danjulio/lepton/ESP32/DesktopApp/pictures/graph_window.png

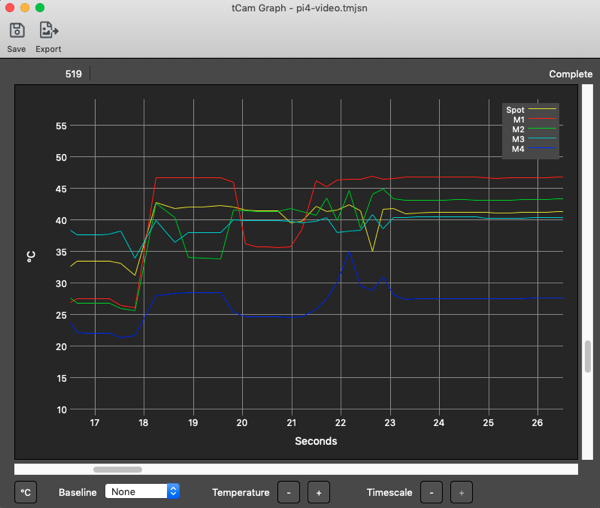
ESP32/DesktopApp/pictures/graph_window.png
