danjulio/lepton/ESP32/tCam-Mini/pictures/hw_if_spi_data.png

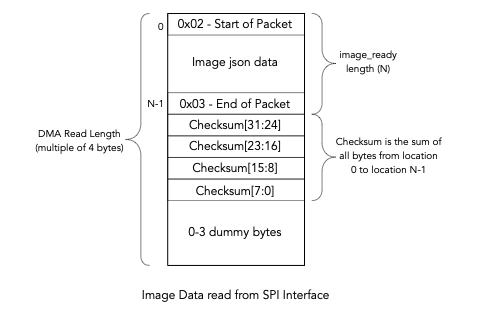
ESP32/tCam-Mini/pictures/hw_if_spi_data.png
