danjulio/lepton/ESP32/tCam-Mini/pictures/tcam_mini_pcb_r1.png

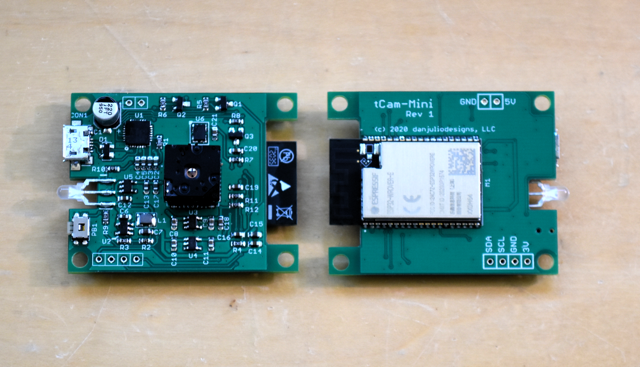
ESP32/tCam-Mini/pictures/tcam_mini_pcb_r1.png
