danjulio/lepton/ESP32/tCam-Mini/pictures/tcam_mini_pcb_r2.png

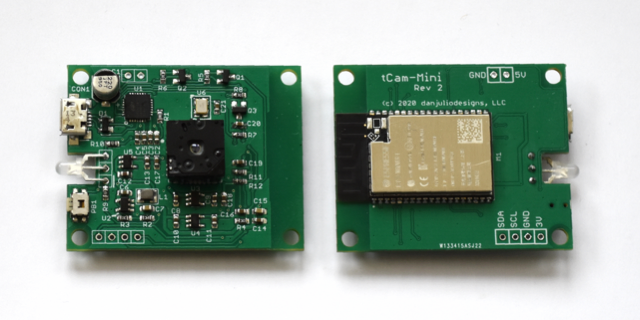
ESP32/tCam-Mini/pictures/tcam_mini_pcb_r2.png
