danjulio/lepton/ESP32/tCam-Mini/pictures/tcam_mini_prototype.png

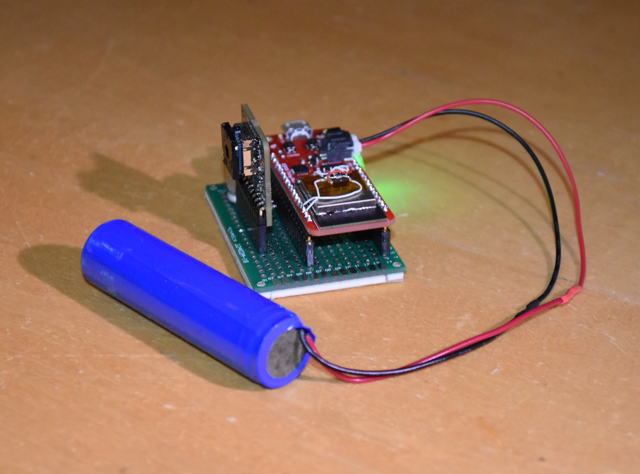
ESP32/tCam-Mini/pictures/tcam_mini_prototype.png
