danjulio/lepton/ESP32/tCam-Mini/pictures/ttgo_based_tcam_mini.png

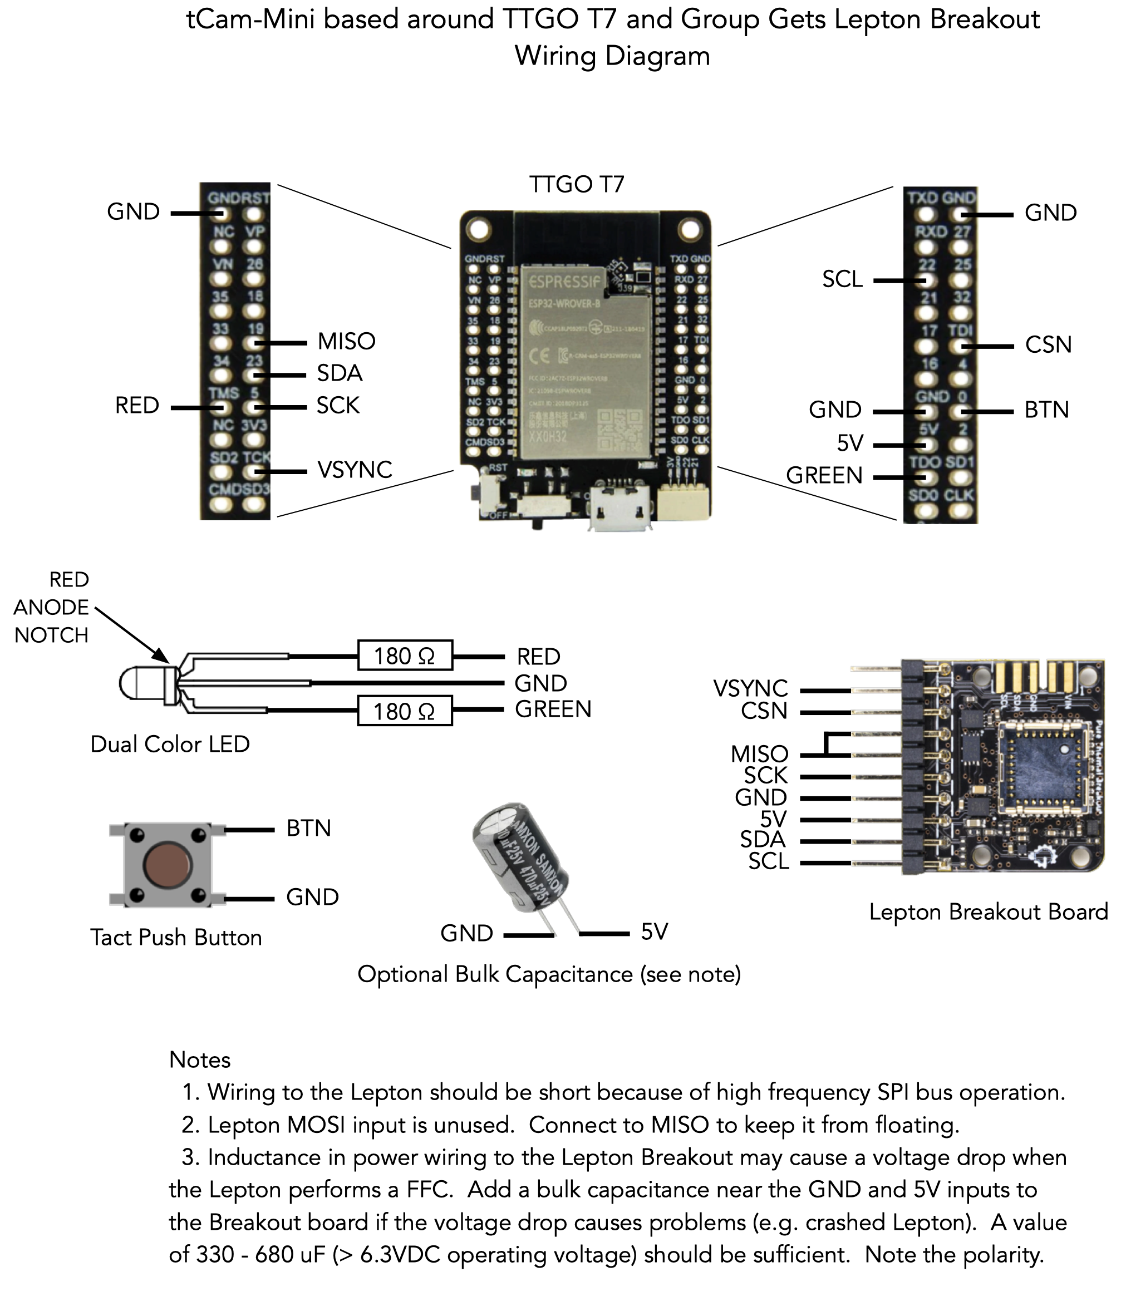
ESP32/tCam-Mini/pictures/ttgo_based_tcam_mini.png
