danjulio/lepton/ESP32/tCam-Mini/pictures/ttgo_version_side.png

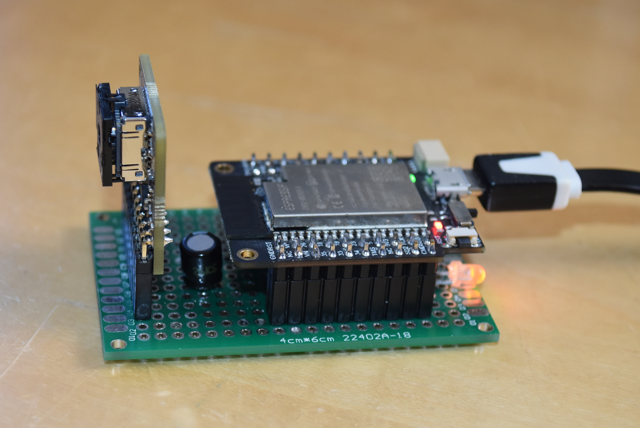
ESP32/tCam-Mini/pictures/ttgo_version_side.png
