danjulio/lepton/ESP32/tCam-Mini/pictures/ttgo_version_top_bot.png

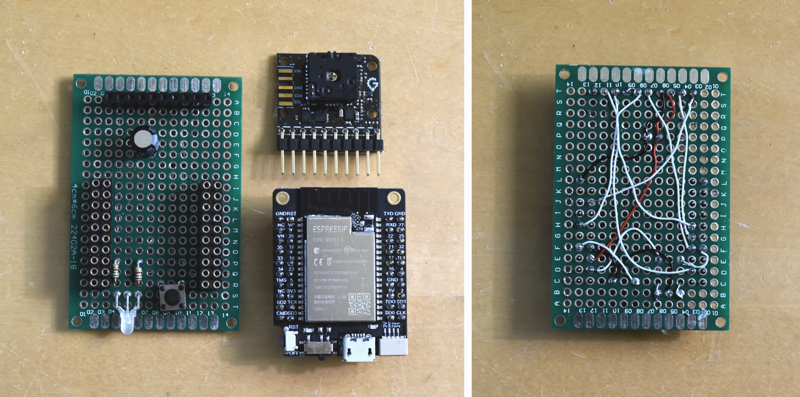
ESP32/tCam-Mini/pictures/ttgo_version_top_bot.png
