danjulio/lepton/ESP32/WebApp/pictures/tcam_analysis.png

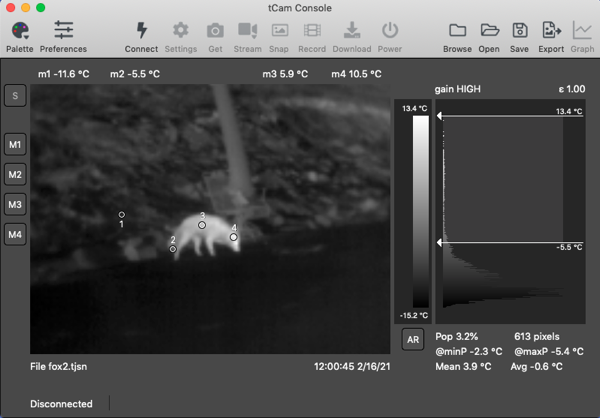
ESP32/WebApp/pictures/tcam_analysis.png
