danjulio/lepton/ESP32/WebApp/pictures/tcam_web_add_camera.png

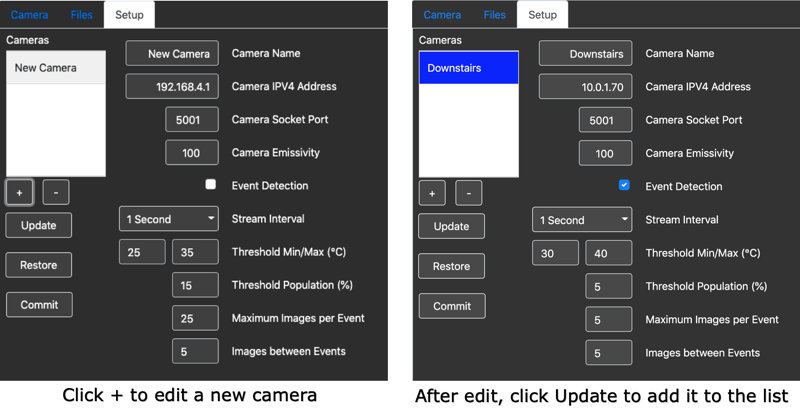
ESP32/WebApp/pictures/tcam_web_add_camera.png
