danjulio/lepton/ESP32/WebApp/pictures/tcam_web_files.png

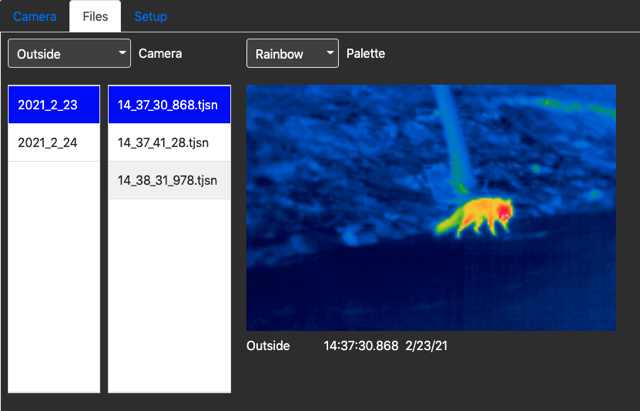
ESP32/WebApp/pictures/tcam_web_files.png
