danjulio/lepton/ESP32/WebApp/pictures/tcam_web_viewer_annotated.png

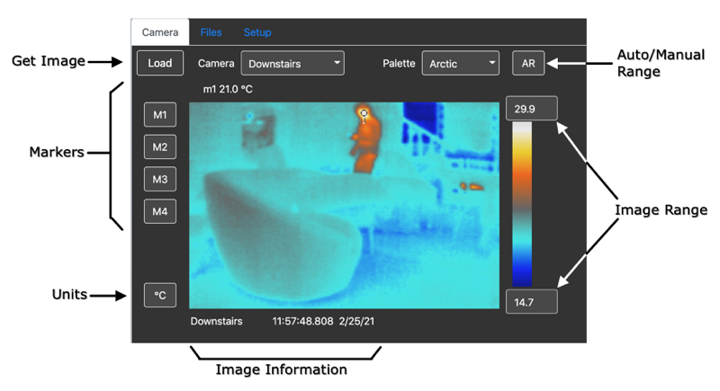
ESP32/WebApp/pictures/tcam_web_viewer_annotated.png
