danjulio/lepton/teensy3/LeptonSDKEmb32OEM/LeptonSDKEmb32OEM.cpp

/*******************************************************************************
**
**   File NAME: LeptonSDKEmb32OEM.cpp
**
**   CREATED: 6/12/2018
**
**   DESCRIPTION: Lepton SDK Module ported to Arduino
**
**   HISTORY: 6/12/2018 DJD - Initial Draft
**           11/22/2019 DJD - Support for ESP32
**
**   Based on FLIR Systems Inc source code.  Their license is copied below
**   and forms the license for this code.
**
**      Copyright 2011,2012,2013,2014 FLIR Systems - Commercial
**      Vision Systems.  All rights reserved.
**
**      Proprietary - PROPRIETARY - FLIR Systems Inc.
**
**      This document is controlled to FLIR Technology Level 2.
**      The information contained in this document pertains to a
**      dual use product Controlled for export by the Export
**      Administration Regulations (EAR). Diversion contrary to
**      US law is prohibited.  US Department of Commerce
**      authorization is not required prior to export or
**      transfer to foreign persons or parties unless otherwise
**      prohibited.
**
**      Redistribution and use in source and binary forms, with
**      or without modification, are permitted provided that the
**      following conditions are met:
**
**      Redistributions of source code must retain the above
**      copyright notice, this list of conditions and the
**      following disclaimer.
**
**      Redistributions in binary form must reproduce the above
**      copyright notice, this list of conditions and the
**      following disclaimer in the documentation and/or other
**      materials provided with the distribution.
**
**      Neither the name of the FLIR Systems Corporation nor the
**      names of its contributors may be used to endorse or
**      promote products derived from this software without
**      specific prior written permission.
**
**      THIS SOFTWARE IS PROVIDED BY THE COPYRIGHT HOLDERS AND
**      CONTRIBUTORS "AS IS" AND ANY EXPRESS OR IMPLIED
**      WARRANTIES, INCLUDING, BUT NOT LIMITED TO, THE IMPLIED
**      WARRANTIES OF MERCHANTABILITY AND FITNESS FOR A
**      PARTICULAR PURPOSE ARE DISCLAIMED. IN NO EVENT SHALL THE
**      COPYRIGHT OWNER OR CONTRIBUTORS BE LIABLE FOR ANY
**      DIRECT, INDIRECT, INCIDENTAL, SPECIAL, EXEMPLARY, OR
**      CONSEQUENTIAL DAMAGES (INCLUDING, BUT NOT LIMITED TO,
**      PROCUREMENT OF SUBSTITUTE GOODS OR SERVICES; LOSS OF
**      USE, DATA, OR PROFITS; OR BUSINESS INTERRUPTION) HOWEVER
**      CAUSED AND ON ANY THEORY OF LIABILITY, WHETHER IN
**      CONTRACT, STRICT LIABILITY, OR TORT (INCLUDING
**      NEGLIGENCE OR OTHERWISE) ARISING IN ANY WAY OUT OF THE
**      USE OF THIS SOFTWARE, EVEN IF ADVISED OF THE POSSIBILITY
**      OF SUCH DAMAGE.
**
*******************************************************************************/
#include "LeptonSDKEmb32OEM.h"
#include <Arduino.h>
#if defined(CORE_TEENSY)
#include <i2c_t3.h>
#else
#include <Wire.h> 
#endif

#if (USE_BORESIGHT_MEASUREMENT_FUNCTIONS == 1)
#include "math.h"
#endif

LeptonSDKEmb32OEM::LeptonSDKEmb32OEM()
{
}


/**************************************/
/*                AGC                 */
/**************************************/

/**
 * Retrieves the current AGC Enable state from the Camera. The 
 * AGC enable state turns AGC On (enabled) or OFF (disabled).   
 * 
 * @param agcEnableStatePtr
 *               Pointer to variable to update with the camera's
 *               current state.
 *               Range:
 *                  LEP_AGC_DISABLE=0
 *                  LEP_AGC_ENABLE =1
 * 
 * @return LEP_OK if all goes well, otherwise an error code.
 */
LEP_RESULT LeptonSDKEmb32OEM::LEP_GetAgcEnableState( LEP_CAMERA_PORT_DESC_T_PTR portDescPtr,
                                  LEP_AGC_ENABLE_E_PTR agcEnableStatePtr )
{
   LEP_RESULT  result = LEP_OK;
   LEP_UINT16 attributeWordLength = 2; /* attribute is an enum, so 32-bit value */

   /* Validate Parameter(s)
   */
   if( agcEnableStatePtr == NULL )
   {
      return( LEP_BAD_ARG_POINTER_ERROR );
   }

   /* Perform Command
   ** Read the Camera's AGC Enable State
   */
   result = LEP_GetAttribute( portDescPtr,
                              ( LEP_COMMAND_ID )LEP_CID_AGC_ENABLE_STATE,
                              ( LEP_ATTRIBUTE_T_PTR )agcEnableStatePtr,
                              attributeWordLength );
   return( result );
}

/**
 * Sets the current AGC Enable state on the Camera.  The 
 * AGC enable state turns AGC On (enabled) or OFF (disabled).
 * 
 * @param agcEnableState 
 *             Specifies the enable state to set the camera' AGC
 *             Range:
 *                LEP_AGC_DISABLE=0
 *                LEP_AGC_ENABLE =1
 * 
 * @return LEP_OK if all goes well, otherwise an error code.
 */
LEP_RESULT LeptonSDKEmb32OEM::LEP_SetAgcEnableState( LEP_CAMERA_PORT_DESC_T_PTR portDescPtr,
                                  LEP_AGC_ENABLE_E agcEnableState )
{
   LEP_RESULT  result = LEP_OK;
   LEP_UINT16 attributeWordLength = 2; /* 2 16-bit value */

   _LEP_data[1] = 0;
   _LEP_data[0] = (LEP_UINT16) agcEnableState;

   /* Validate Parameter(s)
   */
   if( agcEnableState >= LEP_END_AGC_ENABLE )
   {
      return( LEP_RANGE_ERROR );
   }

   /* Perform Command
   ** Writing the Camera's AGC Enable State
   */
   result = LEP_SetAttribute( portDescPtr,
                              ( LEP_COMMAND_ID )LEP_CID_AGC_ENABLE_STATE,
                              ( LEP_ATTRIBUTE_T_PTR ) & _LEP_data,
                              attributeWordLength );
   return( result );
}




LEP_RESULT LeptonSDKEmb32OEM::LEP_GetAgcPolicy( LEP_CAMERA_PORT_DESC_T_PTR portDescPtr,
                             LEP_AGC_POLICY_E_PTR agcPolicyPtr )
{
   LEP_RESULT  result = LEP_OK;
   LEP_UINT16 attributeWordLength = 2; /* 2 16-bit value */

   /* Validate Parameter(s)
   */
   if( agcPolicyPtr == NULL )
   {
      return( LEP_BAD_ARG_POINTER_ERROR );
   }

   /* Perform Command
   ** Reading the Camera's AGC Policy
   */
   result = LEP_GetAttribute(  portDescPtr,
                              ( LEP_COMMAND_ID )LEP_CID_AGC_POLICY,
                              ( LEP_ATTRIBUTE_T_PTR )agcPolicyPtr,
                              attributeWordLength );
   return( result );
}

LEP_RESULT LeptonSDKEmb32OEM::LEP_SetAgcPolicy( LEP_CAMERA_PORT_DESC_T_PTR portDescPtr,
                             LEP_AGC_POLICY_E agcPolicy )
{
   LEP_RESULT  result = LEP_OK;
   LEP_UINT16 attributeWordLength = 2; /* 2 16-bit value */

   _LEP_data[1] = 0;
   _LEP_data[0] = (LEP_UINT16) agcPolicy;

   /* Bounds Check
   */
   if( agcPolicy >= LEP_END_AGC_POLICY )
   {
      return( LEP_RANGE_ERROR );
   }

   /* Perform Command
   ** Writing the Camera's AGC Policy
   */
   result = LEP_SetAttribute( portDescPtr,
                              ( LEP_COMMAND_ID )LEP_CID_AGC_POLICY,
                              ( LEP_ATTRIBUTE_T_PTR ) & _LEP_data,
                              attributeWordLength );
   return( result );
}



LEP_RESULT LeptonSDKEmb32OEM::LEP_GetAgcROI( LEP_CAMERA_PORT_DESC_T_PTR portDescPtr,
                          LEP_AGC_ROI_T_PTR agcROIPtr )
{
   LEP_RESULT  result = LEP_OK;
   LEP_UINT16 attributeWordLength = 4; /* four 16-bit values */

   /* Validate Parameter(s)
   */
   if( agcROIPtr == NULL )
   {
      return( LEP_BAD_ARG_POINTER_ERROR );
   }

   /* Perform Command
   ** Reading the Camera's AGC ROI
   */
   result = LEP_GetAttribute( portDescPtr,
                              ( LEP_COMMAND_ID )LEP_CID_AGC_ROI,
                              ( LEP_ATTRIBUTE_T_PTR )agcROIPtr,
                              attributeWordLength );
   //return(sizeof(*agcROIPtr));
   return( result );
}


LEP_RESULT LeptonSDKEmb32OEM::LEP_SetAgcROI( LEP_CAMERA_PORT_DESC_T_PTR portDescPtr,
                          LEP_AGC_ROI_T agcROI )
{
   LEP_RESULT  result = LEP_OK;
   LEP_UINT16 attributeWordLength = 4; /* four 16-bit values */

   _LEP_data[3] = agcROI.endRow;
   _LEP_data[2] = agcROI.endCol;
   _LEP_data[1] = agcROI.startRow;
   _LEP_data[0] = agcROI.startCol;

   /* Perform Command
   ** Writing the Camera's AGC ROI
   */
   result = LEP_SetAttribute( portDescPtr,
                              ( LEP_COMMAND_ID )LEP_CID_AGC_ROI,
                              ( LEP_ATTRIBUTE_T_PTR ) & _LEP_data,
                              attributeWordLength );


   return( result );
}

LEP_RESULT LeptonSDKEmb32OEM::LEP_GetAgcLinearHistogramClipPercent( LEP_CAMERA_PORT_DESC_T_PTR portDescPtr,
                                                 LEP_UINT16 *agcLinearHistogramClipPercentPtr )
{
   LEP_RESULT  result = LEP_OK;
   LEP_UINT16 attributeWordLength = 1; /* single 16-bit value */

   /* Validate Parameter(s)
   */
   if( agcLinearHistogramClipPercentPtr == NULL )
   {
      return( LEP_BAD_ARG_POINTER_ERROR );
   }

   /* Perform Command
   ** Reading the Camera's AGC Linear Histogram Clip Percent
   */
   result = LEP_GetAttribute( portDescPtr,
                              ( LEP_COMMAND_ID )LEP_CID_AGC_HISTOGRAM_CLIP_PERCENT,
                              ( LEP_ATTRIBUTE_T_PTR )agcLinearHistogramClipPercentPtr,
                              attributeWordLength );
   return( result );
}

LEP_RESULT LeptonSDKEmb32OEM::LEP_SetAgcLinearHistogramClipPercent( LEP_CAMERA_PORT_DESC_T_PTR portDescPtr,
                                                 LEP_UINT16 agcLinearHistogramClipPercent )
{
   LEP_RESULT  result = LEP_OK;
   LEP_UINT16 attributeWordLength = 1; /* single 16-bit value */


   /* Perform Command
   ** Writing the Camera's AGC Linear Histogram Clip Percent
   */
   result = LEP_SetAttribute( portDescPtr,
                              ( LEP_COMMAND_ID )LEP_CID_AGC_HISTOGRAM_CLIP_PERCENT,
                              ( LEP_ATTRIBUTE_T_PTR ) & agcLinearHistogramClipPercent,
                              attributeWordLength
                              );
   return( result );
}


LEP_RESULT LeptonSDKEmb32OEM::LEP_GetAgcLinearHistogramTailSize( LEP_CAMERA_PORT_DESC_T_PTR portDescPtr,
                                              LEP_UINT16 *agcLinearHistogramTailSizePtr )
{
   LEP_RESULT  result = LEP_OK;
   LEP_UINT16 attributeWordLength = 1; /* single 16-bit value */

   /* Validate Parameter(s)
   */
   if( agcLinearHistogramTailSizePtr == NULL )
   {
      return( LEP_BAD_ARG_POINTER_ERROR );
   }

   /* Perform Command
   ** Reading the Camera's AGC Linear Histogram Tail Size
   */
   result = LEP_GetAttribute( portDescPtr,
                              ( LEP_COMMAND_ID )LEP_CID_AGC_HISTOGRAM_TAIL_SIZE,
                              ( LEP_ATTRIBUTE_T_PTR )agcLinearHistogramTailSizePtr,
                              attributeWordLength );
   return( result );
}


LEP_RESULT LeptonSDKEmb32OEM::LEP_SetAgcLinearHistogramTailSize( LEP_CAMERA_PORT_DESC_T_PTR portDescPtr,
                                              LEP_UINT16 agcLinearHistogramTailSize )
{
   LEP_RESULT  result = LEP_OK;
   LEP_UINT16 attributeWordLength = 1; /* single 16-bit value */


   /* Perform Command
   ** Writing the Camera's AGC Linear Histogram Clip Percent
   */
   result = LEP_SetAttribute( portDescPtr,
                              ( LEP_COMMAND_ID )LEP_CID_AGC_HISTOGRAM_TAIL_SIZE,
                              ( LEP_ATTRIBUTE_T_PTR ) & agcLinearHistogramTailSize,
                              attributeWordLength
                              );
   return( result );
}


LEP_RESULT LeptonSDKEmb32OEM::LEP_GetAgcHistogramStatistics( LEP_CAMERA_PORT_DESC_T_PTR portDescPtr,
                                          LEP_AGC_HISTOGRAM_STATISTICS_T_PTR *agcHistogramStatisticsPtr )
{
   LEP_RESULT  result = LEP_OK;
   LEP_UINT16 attributeWordLength = 4; /* four 16-bit values */

   /* Validate Parameter(s)
   */
   if( agcHistogramStatisticsPtr == NULL )
   {
      return( LEP_BAD_ARG_POINTER_ERROR );
   }

   /* Perform Command
   ** Reading the Camera's AGC Linear Histogram Statistics
   */
   result = LEP_GetAttribute( portDescPtr,
                              ( LEP_COMMAND_ID )LEP_CID_AGC_STATISTICS,
                              ( LEP_ATTRIBUTE_T_PTR )agcHistogramStatisticsPtr,
                              attributeWordLength );
   return( result );
}



/* Linear Policy Controls
*/

LEP_RESULT LeptonSDKEmb32OEM::LEP_GetAgcLinearMaxGain( LEP_CAMERA_PORT_DESC_T_PTR portDescPtr,
                                    LEP_UINT16 *agcLinearMaxGainPtr )
{
   LEP_RESULT  result = LEP_OK;
   LEP_UINT16 attributeWordLength = 1; /* single 16-bit value */

   /* Validate Parameter(s)
   */
   if( agcLinearMaxGainPtr == NULL )
   {
      return( LEP_BAD_ARG_POINTER_ERROR );
   }

   /* Perform Command
   ** Reading the Camera's AGC Linear Max Gain
   */
   result = LEP_GetAttribute( portDescPtr,
                              ( LEP_COMMAND_ID )LEP_CID_AGC_LINEAR_MAX_GAIN,
                              ( LEP_ATTRIBUTE_T_PTR )agcLinearMaxGainPtr,
                              attributeWordLength );
   return( result );
}


LEP_RESULT LeptonSDKEmb32OEM::LEP_SetAgcLinearMaxGain( LEP_CAMERA_PORT_DESC_T_PTR portDescPtr,
                                    LEP_UINT16 agcLinearMaxGain )
{
   LEP_RESULT  result = LEP_OK;
   LEP_UINT16 attributeWordLength = 1; /* single 16-bit value */


   /* Perform Command
   ** Writing the Camera's AGC Linear Max Gain
   */
   result = LEP_SetAttribute( portDescPtr,
                              ( LEP_COMMAND_ID )LEP_CID_AGC_LINEAR_MAX_GAIN,
                              ( LEP_ATTRIBUTE_T_PTR ) & agcLinearMaxGain,
                              attributeWordLength
                              );
   return( result );
}


LEP_RESULT LeptonSDKEmb32OEM::LEP_GetAgcLinearMidPoint( LEP_CAMERA_PORT_DESC_T_PTR portDescPtr,
                                     LEP_UINT16 *agcLinearMidPointPtr )
{
   LEP_RESULT  result = LEP_OK;
   LEP_UINT16 attributeWordLength = 1; /* single 16-bit value */

   /* Validate Parameter(s)
   */
   if( agcLinearMidPointPtr == NULL )
   {
      return( LEP_BAD_ARG_POINTER_ERROR );
   }

   /* Perform Command
   ** Reading the Camera's AGC Linear Midpoint
   */
   result = LEP_GetAttribute( portDescPtr,
                              ( LEP_COMMAND_ID )LEP_CID_AGC_LINEAR_MIDPOINT,
                              ( LEP_ATTRIBUTE_T_PTR )agcLinearMidPointPtr,
                              attributeWordLength );
   return( result );
}


LEP_RESULT LeptonSDKEmb32OEM::LEP_SetAgcLinearMidPoint( LEP_CAMERA_PORT_DESC_T_PTR portDescPtr,
                                     LEP_UINT16 agcLinearMidPoint )
{
   LEP_RESULT  result = LEP_OK;
   LEP_UINT16 attributeWordLength = 1; /* single 16-bit value */


   /* Perform Command
   ** Writing the Camera's AGC Linear Midpoint
   */
   result = LEP_SetAttribute( portDescPtr,
                              ( LEP_COMMAND_ID )LEP_CID_AGC_LINEAR_MIDPOINT,
                              ( LEP_ATTRIBUTE_T_PTR ) & agcLinearMidPoint,
                              attributeWordLength
                              );
   return( result );
}


LEP_RESULT LeptonSDKEmb32OEM::LEP_GetAgcLinearDampeningFactor( LEP_CAMERA_PORT_DESC_T_PTR portDescPtr,
                                            LEP_UINT16 *agcLinearDampeningFactorPtr )
{
   LEP_RESULT  result = LEP_OK;
   LEP_UINT16 attributeWordLength = 1; /* single 16-bit value */

   /* Validate Parameter(s)
   */
   if( agcLinearDampeningFactorPtr == NULL )
   {
      return( LEP_BAD_ARG_POINTER_ERROR );
   }

   /* Perform Command
   ** Reading the Camera's AGC Linear Dampening Factor
   */
   result = LEP_GetAttribute( portDescPtr,
                              ( LEP_COMMAND_ID )LEP_CID_AGC_LINEAR_DAMPENING_FACTOR,
                              ( LEP_ATTRIBUTE_T_PTR )agcLinearDampeningFactorPtr,
                              attributeWordLength );
   return( result );
}


LEP_RESULT LeptonSDKEmb32OEM::LEP_SetAgcLinearDampeningFactor( LEP_CAMERA_PORT_DESC_T_PTR portDescPtr,
                                            LEP_UINT16 agcLinearDampeningFactor )
{
   LEP_RESULT  result = LEP_OK;
   LEP_UINT16 attributeWordLength = 1; /* single 16-bit value */


   /* Perform Command
   ** Writing the Camera's AGC Linear Histogram Dampening Factor
   */
   result = LEP_SetAttribute( portDescPtr,
                              ( LEP_COMMAND_ID )LEP_CID_AGC_LINEAR_DAMPENING_FACTOR,
                              ( LEP_ATTRIBUTE_T_PTR ) & agcLinearDampeningFactor,
                              attributeWordLength
                              );
   return( result );
}



/* Heq Policy Controls
*/

LEP_RESULT LeptonSDKEmb32OEM::LEP_GetAgcHeqDampingFactor( LEP_CAMERA_PORT_DESC_T_PTR portDescPtr,
                                       LEP_UINT16 *agcHeqDampingFactorPtr )
{
   LEP_RESULT  result = LEP_OK;
   LEP_UINT16 attributeWordLength = 1; /* single 16-bit value */

   /* Validate Parameter(s)
   */
   if( agcHeqDampingFactorPtr == NULL )
   {
      return( LEP_BAD_ARG_POINTER_ERROR );
   }

   /* Perform Command
   ** Reading the Camera's AGC HEQ Dampening Factor
   */
   result = LEP_GetAttribute( portDescPtr,
                              ( LEP_COMMAND_ID )LEP_CID_AGC_HEQ_DAMPENING_FACTOR,
                              ( LEP_ATTRIBUTE_T_PTR )agcHeqDampingFactorPtr,
                              attributeWordLength );
   return( result );
}


LEP_RESULT LeptonSDKEmb32OEM::LEP_SetAgcHeqDampingFactor( LEP_CAMERA_PORT_DESC_T_PTR portDescPtr,
                                       LEP_UINT16 agcHeqDampingFactor )
{
   LEP_RESULT  result = LEP_OK;
   LEP_UINT16 attributeWordLength = 1; /* single 16-bit value */


   /* Perform Command
   ** Writing the Camera's AGC HEQ Histogram Dampening Factor
   */
   result = LEP_SetAttribute( portDescPtr,
                              ( LEP_COMMAND_ID )LEP_CID_AGC_HEQ_DAMPENING_FACTOR,
                              ( LEP_ATTRIBUTE_T_PTR ) & agcHeqDampingFactor,
                              attributeWordLength
                              );
   return( result );
}


LEP_RESULT LeptonSDKEmb32OEM::LEP_GetAgcHeqMaxGain( LEP_CAMERA_PORT_DESC_T_PTR portDescPtr,
                                 LEP_UINT16 *agcHeqMaxGainPtr )
{
   LEP_RESULT  result = LEP_OK;
   LEP_UINT16 attributeWordLength = 1; /* single 16-bit value */

   /* Validate Parameter(s)
   */
   if( agcHeqMaxGainPtr == NULL )
   {
      return( LEP_BAD_ARG_POINTER_ERROR );
   }

   /* Perform Command
   ** Reading the Camera's AGC HEQ Max Gain
   */
   result = LEP_GetAttribute( portDescPtr,
                              ( LEP_COMMAND_ID )LEP_CID_AGC_HEQ_MAX_GAIN,
                              ( LEP_ATTRIBUTE_T_PTR )agcHeqMaxGainPtr,
                              attributeWordLength );
   return( result );
}


LEP_RESULT LeptonSDKEmb32OEM::LEP_SetAgcHeqMaxGain( LEP_CAMERA_PORT_DESC_T_PTR portDescPtr,
                                 LEP_UINT16 agcHeqMaxGain )
{
   LEP_RESULT  result = LEP_OK;
   LEP_UINT16 attributeWordLength = 1; /* single 16-bit value */


   /* Perform Command
   ** Writing the Camera's AGC HEQ Max Gain
   */
   result = LEP_SetAttribute( portDescPtr,
                              ( LEP_COMMAND_ID )LEP_CID_AGC_HEQ_MAX_GAIN,
                              ( LEP_ATTRIBUTE_T_PTR ) & agcHeqMaxGain,
                              attributeWordLength
                              );
   return( result );
}


LEP_RESULT LeptonSDKEmb32OEM::LEP_GetAgcHeqClipLimitHigh( LEP_CAMERA_PORT_DESC_T_PTR portDescPtr,
                                       LEP_UINT16 *agcHeqClipLimitHighPtr )
{
   LEP_RESULT  result = LEP_OK;
   LEP_UINT16 attributeWordLength = 1; /* single 16-bit value */

   /* Validate Parameter(s)
   */
   if( agcHeqClipLimitHighPtr == NULL )
   {
      return( LEP_BAD_ARG_POINTER_ERROR );
   }

   /* Perform Command
   ** Reading the Camera's AGC HEQ Clip Limit High
   */
   result = LEP_GetAttribute( portDescPtr,
                              ( LEP_COMMAND_ID )LEP_CID_AGC_HEQ_CLIP_LIMIT_HIGH,
                              ( LEP_ATTRIBUTE_T_PTR )agcHeqClipLimitHighPtr,
                              attributeWordLength );

   return( result );
}


LEP_RESULT LeptonSDKEmb32OEM::LEP_SetAgcHeqClipLimitHigh( LEP_CAMERA_PORT_DESC_T_PTR portDescPtr,
                                       LEP_UINT16 agcHeqClipLimitHigh )
{
   LEP_RESULT  result = LEP_OK;
   LEP_UINT16 attributeWordLength = 1; /* single 16-bit value */


   /* Perform Command
   ** Writing the Camera's AGC HEQ Clip Limit High
   */
   result = LEP_SetAttribute( portDescPtr,
                              ( LEP_COMMAND_ID )LEP_CID_AGC_HEQ_CLIP_LIMIT_HIGH,
                              ( LEP_ATTRIBUTE_T_PTR ) & agcHeqClipLimitHigh,
                              attributeWordLength
                              );
   return( result );
}


LEP_RESULT LeptonSDKEmb32OEM::LEP_GetAgcHeqClipLimitLow( LEP_CAMERA_PORT_DESC_T_PTR portDescPtr,
                                      LEP_UINT16 *agcHeqClipLimitLowPtr )
{
   LEP_RESULT  result = LEP_OK;
   LEP_UINT16 attributeWordLength = 1; /* single 16-bit value */

   /* Validate Parameter(s)
   */
   if( agcHeqClipLimitLowPtr == NULL )
   {
      return( LEP_BAD_ARG_POINTER_ERROR );
   }

   /* Perform Command
   ** Reading the Camera's AGC HEQ Clip Limit Low
   */
   result = LEP_GetAttribute( portDescPtr,
                              ( LEP_COMMAND_ID )LEP_CID_AGC_HEQ_CLIP_LIMIT_LOW,
                              ( LEP_ATTRIBUTE_T_PTR )agcHeqClipLimitLowPtr,
                              attributeWordLength );
   return( result );
}


LEP_RESULT LeptonSDKEmb32OEM::LEP_SetAgcHeqClipLimitLow( LEP_CAMERA_PORT_DESC_T_PTR portDescPtr,
                                      LEP_UINT16 agcHeqClipLimitLow )
{
   LEP_RESULT  result = LEP_OK;
   LEP_UINT16 attributeWordLength = 1; /* single 16-bit value */


   /* Perform Command
   ** Writing the Camera's AGC HEQ Clip Limit Low
   */
   result = LEP_SetAttribute( portDescPtr,
                              ( LEP_COMMAND_ID )LEP_CID_AGC_HEQ_CLIP_LIMIT_LOW,
                              ( LEP_ATTRIBUTE_T_PTR ) & agcHeqClipLimitLow,
                              attributeWordLength
                              );
   return( result );
}


LEP_RESULT LeptonSDKEmb32OEM::LEP_GetAgcHeqBinExtension( LEP_CAMERA_PORT_DESC_T_PTR portDescPtr,
                                      LEP_UINT16 *agcHeqBinExtensionPtr )
{
   LEP_RESULT  result = LEP_OK;
   LEP_UINT16 attributeWordLength = 1; /* single 16-bit value */

   /* Validate Parameter(s)
   */
   if( agcHeqBinExtensionPtr == NULL )
   {
      return( LEP_BAD_ARG_POINTER_ERROR );
   }

   /* Perform Command
   ** Reading the Camera's AGC HEQ Bin Extension
   */
   result = LEP_GetAttribute( portDescPtr,
                              ( LEP_COMMAND_ID )LEP_CID_AGC_HEQ_BIN_EXTENSION,
                              ( LEP_ATTRIBUTE_T_PTR )agcHeqBinExtensionPtr,
                              attributeWordLength );
   return( result );
}


LEP_RESULT LeptonSDKEmb32OEM::LEP_SetAgcHeqBinExtension( LEP_CAMERA_PORT_DESC_T_PTR portDescPtr,
                                      LEP_UINT16 agcHeqBinExtension )
{
   LEP_RESULT  result = LEP_OK;
   LEP_UINT16 attributeWordLength = 1; /* single 16-bit value */


   /* Perform Command
   ** Writing the Camera's AGC HEQ Bin Extension
   */
   result = LEP_SetAttribute( portDescPtr,
                              ( LEP_COMMAND_ID )LEP_CID_AGC_HEQ_BIN_EXTENSION,
                              ( LEP_ATTRIBUTE_T_PTR ) & agcHeqBinExtension,
                              attributeWordLength
                              );
   return( result );
}


LEP_RESULT LeptonSDKEmb32OEM::LEP_GetAgcHeqMidPoint( LEP_CAMERA_PORT_DESC_T_PTR portDescPtr,
                                  LEP_UINT16 *agcHeqMidPointPtr )
{
   LEP_RESULT  result = LEP_OK;
   LEP_UINT16 attributeWordLength = 1; /* single 16-bit value */

   /* Validate Parameter(s)
   */
   if( agcHeqMidPointPtr == NULL )
   {
      return( LEP_BAD_ARG_POINTER_ERROR );
   }

   /* Perform Command
   ** Reading the Camera's AGC HEQ Midpoint
   */
   result = LEP_GetAttribute( portDescPtr,
                              ( LEP_COMMAND_ID )LEP_CID_AGC_HEQ_MIDPOINT,
                              ( LEP_ATTRIBUTE_T_PTR )agcHeqMidPointPtr,
                              attributeWordLength );
   return( result );
}


LEP_RESULT LeptonSDKEmb32OEM::LEP_SetAgcHeqMidPoint( LEP_CAMERA_PORT_DESC_T_PTR portDescPtr,
                                  LEP_UINT16 agcHeqMidPoint )
{
   LEP_RESULT  result = LEP_OK;
   LEP_UINT16 attributeWordLength = 1; /* single 16-bit value */


   /* Perform Command
   ** Writing the Camera's AGC HEQ Midpoint
   */
   result = LEP_SetAttribute( portDescPtr,
                              ( LEP_COMMAND_ID )LEP_CID_AGC_HEQ_MIDPOINT,
                              ( LEP_ATTRIBUTE_T_PTR ) & agcHeqMidPoint,
                              attributeWordLength
                              );
   return( result );
}

LEP_RESULT LeptonSDKEmb32OEM::LEP_GetAgcHeqEmptyCount( LEP_CAMERA_PORT_DESC_T_PTR portDescPtr,
                                    LEP_AGC_HEQ_EMPTY_COUNT_T_PTR emptyCountPtr )
{
   LEP_RESULT result = LEP_OK;
   LEP_UINT16 attributeWordLength = 1;

   result = LEP_GetAttribute( portDescPtr,
                              ( LEP_COMMAND_ID )LEP_CID_AGC_HEQ_EMPTY_COUNTS,
                              ( LEP_ATTRIBUTE_T_PTR )emptyCountPtr,
                              attributeWordLength );

   return( result );
}
LEP_RESULT LeptonSDKEmb32OEM::LEP_SetAgcHeqEmptyCount( LEP_CAMERA_PORT_DESC_T_PTR portDescPtr,
                                    LEP_AGC_HEQ_EMPTY_COUNT_T emptyCount )
{
   LEP_RESULT result = LEP_OK;
   LEP_UINT16 attributeWordLength = 1;

   result = LEP_SetAttribute( portDescPtr,
                              ( LEP_COMMAND_ID )LEP_CID_AGC_HEQ_EMPTY_COUNTS,
                              ( LEP_ATTRIBUTE_T_PTR ) & emptyCount,
                              attributeWordLength );

   return( result );
}

LEP_RESULT LeptonSDKEmb32OEM::LEP_GetAgcHeqNormalizationFactor( LEP_CAMERA_PORT_DESC_T_PTR portDescPtr,
                                             LEP_AGC_HEQ_NORMALIZATION_FACTOR_T_PTR normalizationFactorPtr )
{
   LEP_RESULT result = LEP_OK;
   LEP_UINT16 attributeWordLength = 1;

   result = LEP_GetAttribute( portDescPtr,
                              ( LEP_COMMAND_ID )LEP_CID_AGC_HEQ_NORMALIZATION_FACTOR,
                              ( LEP_ATTRIBUTE_T_PTR )normalizationFactorPtr,
                              attributeWordLength );

   return( result );
}
LEP_RESULT LeptonSDKEmb32OEM::LEP_SetAgcHeqNormalizationFactor( LEP_CAMERA_PORT_DESC_T_PTR portDescPtr,
                                             LEP_AGC_HEQ_NORMALIZATION_FACTOR_T normalizationFactor )
{
   LEP_RESULT result = LEP_OK;
   LEP_UINT16 attributeWordLength = 1;

   result = LEP_SetAttribute( portDescPtr,
                              ( LEP_COMMAND_ID )LEP_CID_AGC_HEQ_NORMALIZATION_FACTOR,
                              ( LEP_ATTRIBUTE_T_PTR ) & normalizationFactor,
                              attributeWordLength );

   return( result );
}

LEP_RESULT LeptonSDKEmb32OEM::LEP_GetAgcHeqScaleFactor( LEP_CAMERA_PORT_DESC_T_PTR portDescPtr,
                                     LEP_AGC_HEQ_SCALE_FACTOR_E_PTR scaleFactorPtr )
{
   LEP_RESULT result = LEP_OK;
   LEP_UINT16 attributeWordLength = 2;    /* enums are 32-bit */

   result = LEP_GetAttribute( portDescPtr,
                              ( LEP_COMMAND_ID )LEP_CID_AGC_HEQ_SCALE_FACTOR,
                              ( LEP_ATTRIBUTE_T_PTR )scaleFactorPtr,
                              attributeWordLength );

   return( result );
}
LEP_RESULT LeptonSDKEmb32OEM::LEP_SetAgcHeqScaleFactor( LEP_CAMERA_PORT_DESC_T_PTR portDescPtr,
                                     LEP_AGC_HEQ_SCALE_FACTOR_E scaleFactor )
{
   LEP_RESULT result = LEP_OK;
   LEP_UINT16 attributeWordLength = 2;    /* enums are 32-bit */

   _LEP_data[1] = 0;
   _LEP_data[0] = (LEP_UINT16) scaleFactor;

   result = LEP_SetAttribute( portDescPtr,
                              ( LEP_COMMAND_ID )LEP_CID_AGC_HEQ_SCALE_FACTOR,
                              ( LEP_ATTRIBUTE_T_PTR ) & _LEP_data,
                              attributeWordLength );

   return( result );
}


LEP_RESULT LeptonSDKEmb32OEM::LEP_GetAgcCalcEnableState( LEP_CAMERA_PORT_DESC_T_PTR portDescPtr,
                                      LEP_AGC_ENABLE_E_PTR agcCalculationEnableStatePtr )
{
   LEP_RESULT result = LEP_OK;
   LEP_UINT16 attributeWordLength = 2;

   if( agcCalculationEnableStatePtr == NULL )
   {
      return( LEP_BAD_ARG_POINTER_ERROR );
   }

   result = LEP_GetAttribute( portDescPtr,
                              ( LEP_COMMAND_ID )LEP_CID_AGC_CALC_ENABLE_STATE,
                              ( LEP_ATTRIBUTE_T_PTR )agcCalculationEnableStatePtr,
                              attributeWordLength );

   return( result );
}
LEP_RESULT LeptonSDKEmb32OEM::LEP_SetAgcCalcEnableState( LEP_CAMERA_PORT_DESC_T_PTR portDescPtr,
                                      LEP_AGC_ENABLE_E agcCalculationEnableState )
{
   LEP_RESULT result = LEP_OK;
   LEP_UINT16 attributeWordLength = 2;

   _LEP_data[1] = 0;
   _LEP_data[0] = (LEP_UINT16) agcCalculationEnableState;

   if( agcCalculationEnableState >= LEP_END_AGC_ENABLE )
   {
      return( LEP_RANGE_ERROR );
   }

   result = LEP_SetAttribute( portDescPtr,
                              ( LEP_COMMAND_ID )LEP_CID_AGC_CALC_ENABLE_STATE,
                              ( LEP_ATTRIBUTE_T_PTR ) & _LEP_data,
                              attributeWordLength );

   return( result );
}

LEP_RESULT LeptonSDKEmb32OEM::LEP_GetAgcHeqLinearPercent( LEP_CAMERA_PORT_DESC_T_PTR portDescPtr,
                                       LEP_UINT16 *agcHeqLinearPercentPtr)
{
   LEP_RESULT result = LEP_OK;
   LEP_UINT16 attributeWordLength = 1;

   if( agcHeqLinearPercentPtr == NULL )
   {
      return( LEP_BAD_ARG_POINTER_ERROR );
   }

   result = LEP_GetAttribute( portDescPtr,
                              ( LEP_COMMAND_ID )LEP_CID_AGC_HEQ_LINEAR_PERCENT,
                              ( LEP_ATTRIBUTE_T_PTR )agcHeqLinearPercentPtr,
                              attributeWordLength );

   return(result);
}

LEP_RESULT LeptonSDKEmb32OEM::LEP_SetAgcHeqLinearPercent( LEP_CAMERA_PORT_DESC_T_PTR portDescPtr,
                                       LEP_UINT16 agcHeqLinearPercent)
{
   LEP_RESULT result = LEP_OK;
   LEP_UINT16 attributeWordLength = 1;

   result = LEP_SetAttribute( portDescPtr,
                              ( LEP_COMMAND_ID )LEP_CID_AGC_HEQ_LINEAR_PERCENT,
                              ( LEP_ATTRIBUTE_T_PTR )&agcHeqLinearPercent,
                              attributeWordLength );

   return(result);
}


/**************************************/
/*           I2C_Protocol             */
/**************************************/
LEP_RESULT LeptonSDKEmb32OEM::LEP_I2C_SelectDevice(LEP_CAMERA_PORT_DESC_T_PTR portDescPtr, 
                                LEP_PROTOCOL_DEVICE_E device)
{
    LEP_RESULT result;

    result = LEP_I2C_MasterSelectDevice( portDescPtr, device );

    return(result);
}

LEP_RESULT LeptonSDKEmb32OEM::LEP_I2C_OpenPort(LEP_UINT16 portID,
                            LEP_UINT16 *baudRateInkHz,
                            LEP_UINT8* deviceAddress)
{
   LEP_RESULT result;
   LEP_UINT16 statusReg;

   result = LEP_I2C_MasterOpen( portID, baudRateInkHz );

   if(result != LEP_OK)
   {
      return(LEP_COMM_INVALID_PORT_ERROR);
   }

   *deviceAddress = 0x2a;
   result = LEP_I2C_MasterReadData( portID,
                                *deviceAddress,
                                LEP_I2C_STATUS_REG,
                                &statusReg,
                                1 );
   
   if(result != LEP_OK)
   {
      /*
       *    Try 0x00 as the device address if 0x2a didn't work. In this case, we are in Virgin Boot Mode.
       *
       */
      *deviceAddress = 0x00;
      result = LEP_I2C_MasterReadData( portID,
                                   *deviceAddress,
                                   LEP_I2C_STATUS_REG,
                                   &statusReg,
                                   1 );
      if(result != LEP_OK)
      {
         return(LEP_COMM_NO_DEV);
      }
   }

    return(result);
}


LEP_RESULT LeptonSDKEmb32OEM::LEP_I2C_ClosePort(LEP_CAMERA_PORT_DESC_T_PTR portDescPtr)
{
    LEP_RESULT result;

    result =LEP_I2C_MasterClose( portDescPtr );

    return(result);
}


LEP_RESULT LeptonSDKEmb32OEM::LEP_I2C_ResetPort(LEP_CAMERA_PORT_DESC_T_PTR portDescPtr)
{
    LEP_RESULT result;

    result = LEP_I2C_MasterReset( portDescPtr );

    return(result);
}


LEP_RESULT LeptonSDKEmb32OEM::LEP_I2C_GetAttribute(LEP_CAMERA_PORT_DESC_T_PTR portDescPtr,
                                LEP_COMMAND_ID commandID, 
                                LEP_ATTRIBUTE_T_PTR attributePtr,
                                LEP_UINT16 attributeWordLength)
{
    LEP_RESULT result;
    LEP_UINT16 statusReg;
    LEP_INT16 statusCode;
    LEP_UINT32 done;
    LEP_UINT16 crcExpected, crcActual;

    /* Implement the Lepton TWI READ Protocol
    */
    /* First wait until the Camera is ready to receive a new
    ** command by polling the STATUS REGISTER BUSY Bit until it
    ** reports NOT BUSY.
    */ 

    do
    {
        /* Read the Status REGISTER and peek at the BUSY Bit
        */ 
        result = LEP_I2C_MasterReadData( portDescPtr->portID,
                                         portDescPtr->deviceAddress,
                                         LEP_I2C_STATUS_REG,
                                         &statusReg,
                                         1 );
        if(result != LEP_OK)
        {
           return(result);
        }
        done = (statusReg & LEP_I2C_STATUS_BUSY_BIT_MASK)? 0: 1;

    }while( !done );

    /* Set the Lepton's DATA LENGTH REGISTER first to inform the
    ** Lepton Camera how many 16-bit DATA words we want to read.
    */ 
    result = LEP_I2C_MasterWriteData( portDescPtr->portID,
                                      portDescPtr->deviceAddress,
                                      LEP_I2C_DATA_LENGTH_REG, 
                                      &attributeWordLength, 
                                      1);
    if(result != LEP_OK)
    {
       return(result);
    }
    /* Now issue the GET Attribute Command
    */ 
    result = LEP_I2C_MasterWriteData( portDescPtr->portID,
                                      portDescPtr->deviceAddress,
                                      LEP_I2C_COMMAND_REG, 
                                      &commandID, 
                                      1);

    if(result != LEP_OK)
    {
       return(result);
    }

    /* Now wait until the Camera has completed this command by
    ** polling the statusReg REGISTER BUSY Bit until it reports NOT
    ** BUSY.
    */ 
    do
    {
        /* Read the statusReg REGISTER and peek at the BUSY Bit
        */ 
        result = LEP_I2C_MasterReadData( portDescPtr->portID,
                                         portDescPtr->deviceAddress,
                                         LEP_I2C_STATUS_REG,
                                         &statusReg,
                                         1 );

        if(result != LEP_OK)
        {
           return(result);
        }
        done = (statusReg & LEP_I2C_STATUS_BUSY_BIT_MASK)? 0: 1;

    }while( !done );
    

    /* Check statusReg word for Errors?
    */ 
    statusCode = (statusReg >> 8) ? ((statusReg >> 8) | 0xFF00) : 0;
    if(statusCode)
    {
      return((LEP_RESULT)statusCode);
    }

    /* If NO Errors then READ the DATA from the DATA REGISTER(s)
    */ 
    if( attributeWordLength <= 16 )
    {
        /* Read from the DATA Registers - always start from DATA 0
        ** Little Endean
        */ 
        result = LEP_I2C_MasterReadData(portDescPtr->portID,
                                        portDescPtr->deviceAddress,
                                        LEP_I2C_DATA_0_REG,
                                        attributePtr,
                                        attributeWordLength );
    }
    else if( attributeWordLength <= 1024 )
    {
        /* Read from the DATA Block Buffer
        */ 
      result = LEP_I2C_MasterReadData(portDescPtr->portID,
                                      portDescPtr->deviceAddress,
                                      LEP_I2C_DATA_BUFFER_0,
                                      attributePtr,
                                      attributeWordLength );
    }

//    if(result == LEP_OK && attributeWordLength > 0)
//    {
//       /* Check CRC */
//       result = LEP_I2C_MasterReadData( portDescPtr->portID,
//                                        portDescPtr->deviceAddress,
//                                        LEP_I2C_DATA_CRC_REG,
//                                        &crcExpected,
//                                        1);
//       crcActual = (LEP_UINT16)CalcCRC16Words(attributeWordLength, (short*)attributePtr);
//
//       /* Check for 0 in the register in case the camera does not support CRC check
//       */
//       if(crcExpected != 0 && crcExpected != crcActual)
//       {
//          return(LEP_CHECKSUM_ERROR);
//       }
//       
//    }

    return(result);
}


LEP_RESULT LeptonSDKEmb32OEM::LEP_I2C_SetAttribute(LEP_CAMERA_PORT_DESC_T_PTR portDescPtr,
                                LEP_COMMAND_ID commandID, 
                                LEP_ATTRIBUTE_T_PTR attributePtr,
                                LEP_UINT16 attributeWordLength)
{
    LEP_RESULT result;
    LEP_UINT16 statusReg;
    LEP_INT16 statusCode;
    LEP_UINT32 done;
    LEP_UINT16 timeoutCount = LEPTON_I2C_COMMAND_BUSY_WAIT_COUNT;

    /* Implement the Lepton TWI WRITE Protocol
    */
    /* First wait until the Camera is ready to receive a new
    ** command by polling the STATUS REGISTER BUSY Bit until it
    ** reports NOT BUSY.
    */ 
    do
    {
        /* Read the Status REGISTER and peek at the BUSY Bit
        */ 
        result = LEP_I2C_MasterReadData( portDescPtr->portID,
                                         portDescPtr->deviceAddress,
                                         LEP_I2C_STATUS_REG,
                                         &statusReg,
                                         1 );
        if(result != LEP_OK)
        {
           return(result);
        }
        done = (statusReg & LEP_I2C_STATUS_BUSY_BIT_MASK)? 0: 1;
        /* Add timout check */
        if( timeoutCount-- == 0 )
        {
            /* Timed out waiting for command busy to go away
            */ 
          return(LEP_TIMEOUT_ERROR);

        }
    }while( !done );

    if( result == LEP_OK )
    {
        /* Now WRITE the DATA to the DATA REGISTER(s)
        */ 
        if( attributeWordLength <= 16 )
        {
            /* WRITE to the DATA Registers - always start from DATA 0
            */ 
            result = LEP_I2C_MasterWriteData(portDescPtr->portID,
                                             portDescPtr->deviceAddress,
                                             LEP_I2C_DATA_0_REG,
                                             attributePtr,
                                             attributeWordLength );
        }
        else if( attributeWordLength <= 1024 )
        {
            /* WRITE to the DATA Block Buffer
            */     
            result = LEP_I2C_MasterWriteData(portDescPtr->portID,
                                             portDescPtr->deviceAddress,
                                             LEP_I2C_DATA_BUFFER_0,
                                             attributePtr,
                                             attributeWordLength );

        }
        else
            result = LEP_RANGE_ERROR;
    }

    if( result == LEP_OK )
    {
        /* Set the Lepton's DATA LENGTH REGISTER first to inform the
        ** Lepton Camera how many 16-bit DATA words we want to read.
        */ 
        result = LEP_I2C_MasterWriteData( portDescPtr->portID,
                                          portDescPtr->deviceAddress,
                                          LEP_I2C_DATA_LENGTH_REG, 
                                          &attributeWordLength, 
                                          1);

        if( result == LEP_OK )
        {
            /* Now issue the SET Attribute Command
            */ 
            result = LEP_I2C_MasterWriteData( portDescPtr->portID,
                                              portDescPtr->deviceAddress,
                                              LEP_I2C_COMMAND_REG, 
                                              &commandID, 
                                              1);
			
            if( result == LEP_OK )
            {
                /* Now wait until the Camera has completed this command by
                ** polling the statusReg REGISTER BUSY Bit until it reports NOT
                ** BUSY.
                */ 
                do
                {
                    /* Read the statusReg REGISTER and peek at the BUSY Bit
                    */ 
                    result = LEP_I2C_MasterReadData( portDescPtr->portID,
                                                     portDescPtr->deviceAddress,
                                                     LEP_I2C_STATUS_REG,
                                                     &statusReg,
                                                     1 );
                    if(result != LEP_OK)
                    {
                       return(result);
                    }
                    done = (statusReg & LEP_I2C_STATUS_BUSY_BIT_MASK)? 0: 1;

                }while( !done );

                    /* Check statusReg word for Errors?
                   */ 
                   statusCode = (statusReg >> 8) ? ((statusReg >> 8) | 0xFF00) : 0;
                   if(statusCode)
                   {
                     return((LEP_RESULT)statusCode);
                   }

            }
        }
    }

    /* Check statusReg word for Errors?
    */

    return(result);
}


LEP_RESULT LeptonSDKEmb32OEM::LEP_I2C_RunCommand(LEP_CAMERA_PORT_DESC_T_PTR portDescPtr,
                              LEP_COMMAND_ID commandID)
{
    LEP_RESULT result;
    LEP_UINT16 statusReg;
    LEP_INT16 statusCode;
    LEP_UINT32 done;
    LEP_UINT16 timeoutCount = LEPTON_I2C_COMMAND_BUSY_WAIT_COUNT;

    /* Implement the Lepton TWI WRITE Protocol
    */
    /* First wait until the Camera is ready to receive a new
    ** command by polling the STATUS REGISTER BUSY Bit until it
    ** reports NOT BUSY.
    */ 
    do
    {
        /* Read the Status REGISTER and peek at the BUSY Bit
        */ 
        result = LEP_I2C_MasterReadRegister( portDescPtr->portID,
                                             portDescPtr->deviceAddress,
                                             LEP_I2C_STATUS_REG,
                                             &statusReg);
        if(result != LEP_OK)
        {
            return(result);
        }
        done = (statusReg & LEP_I2C_STATUS_BUSY_BIT_MASK)? 0: 1;
        /* Add timout check */
        if( timeoutCount-- == 0 )
        {
            /* Timed out waiting for command busy to go away
            */ 

        }
    }while( !done );

    if( result == LEP_OK )
    {
        /* Set the Lepton's DATA LENGTH REGISTER first to inform the
        ** Lepton Camera no 16-bit DATA words being transferred.
        */ 
        result = LEP_I2C_MasterWriteRegister( portDescPtr->portID,
                                              portDescPtr->deviceAddress,
                                              LEP_I2C_DATA_LENGTH_REG, 
                                              (LEP_UINT16)0);

        if( result == LEP_OK )
        {
            /* Now issue the Run Command
            */ 
            result = LEP_I2C_MasterWriteRegister( portDescPtr->portID,
                                                  portDescPtr->deviceAddress,
                                                  LEP_I2C_COMMAND_REG, 
                                                  commandID);
            if( result == LEP_OK )
            {
                /* Now wait until the Camera has completed this command by
                ** polling the statusReg REGISTER BUSY Bit until it reports NOT
                ** BUSY.
                */ 
                do
                {
                    /* Read the statusReg REGISTER and peek at the BUSY Bit
                    */ 
                    result = LEP_I2C_MasterReadRegister( portDescPtr->portID,
                                                         portDescPtr->deviceAddress,
                                                         LEP_I2C_STATUS_REG,
                                                         &statusReg);
                    if(result != LEP_OK)
                    {
                        return(result);
                    }
                    done = (statusReg & LEP_I2C_STATUS_BUSY_BIT_MASK)? 0: 1;
                    /* Timeout? */

                }while( !done );

                statusCode = (statusReg >> 8) ? ((statusReg >> 8) | 0xFF00) : 0;
                if(statusCode)
                {
                  return((LEP_RESULT)statusCode);
                }
            }
        }
    }

    /* Check statusReg word for Errors?
    */

    
    return(result);
}

LEP_RESULT LeptonSDKEmb32OEM::LEP_I2C_DirectReadRegister(LEP_CAMERA_PORT_DESC_T_PTR portDescPtr,
                                      LEP_UINT16 regAddress,
                                      LEP_UINT16 *regValue)
{
   LEP_RESULT result = LEP_OK;

   result = LEP_I2C_MasterReadRegister( portDescPtr->portID,
                                        portDescPtr->deviceAddress,
                                        regAddress,
                                        regValue);

   return(result);
}

LEP_RESULT LeptonSDKEmb32OEM::LEP_I2C_GetPortStatus(LEP_CAMERA_PORT_DESC_T_PTR portDescPtr)
{
    LEP_RESULT result = LEP_OK;

    return(result);
}

LEP_RESULT LeptonSDKEmb32OEM::LEP_I2C_GetDeviceAddress(LEP_CAMERA_PORT_DESC_T_PTR portDescPtr,
                                    LEP_UINT8* deviceAddress)
{
   LEP_RESULT result = LEP_OK;

   if(deviceAddress == NULL)
   {
      return(LEP_BAD_ARG_POINTER_ERROR);
   }
   *deviceAddress = portDescPtr->deviceAddress;

   return(result);
}


LEP_RESULT LeptonSDKEmb32OEM::LEP_I2C_DirectWriteBuffer(LEP_CAMERA_PORT_DESC_T_PTR portDescPtr,
                                     LEP_ATTRIBUTE_T_PTR attributePtr,
                                     LEP_UINT16 attributeWordLength)
{
   LEP_RESULT result = LEP_OK;

   /* WRITE to the DATA Block Buffer
   */     
   result = LEP_I2C_MasterWriteData(portDescPtr->portID,
                                    portDescPtr->deviceAddress,
                                    LEP_I2C_DATA_BUFFER_0,
                                    attributePtr,
                                    attributeWordLength );

  

   return(result);
}

LEP_RESULT LeptonSDKEmb32OEM::LEP_I2C_DirectWriteRegister(LEP_CAMERA_PORT_DESC_T_PTR portDescPtr,
                                       LEP_UINT16 regAddress,
                                       LEP_UINT16 regValue)
{
   LEP_RESULT result = LEP_OK;

   result = LEP_I2C_MasterWriteRegister(portDescPtr->portID,
                                        portDescPtr->deviceAddress,
                                        regAddress, 
                                        regValue);
   return(result);
}


/**************************************/
/*            I2C_Service             */
/**************************************/
LEP_RESULT LeptonSDKEmb32OEM::LEP_I2C_MasterSelectDevice(LEP_CAMERA_PORT_DESC_T_PTR portDescPtr, 
                                      LEP_PROTOCOL_DEVICE_E device)
{
    LEP_RESULT result = LEP_OK;

    /* Do any device-specific calls to implement a close operation
    */ 
#ifdef IMPLEMENTS_SELECT_DEVICE
	result = DEV_I2C_MasterSelectDevice(device);
#else
    result = LEP_UNDEFINED_FUNCTION_ERROR;
#endif

    return(result);
}

/* Driver Open
*/ 
LEP_RESULT LeptonSDKEmb32OEM::LEP_I2C_MasterOpen(LEP_UINT16 portID, 
                              LEP_UINT16 *portBaudRate)
{
    LEP_RESULT result;

    /* Call the I2C Device-Specific Driver to open device as a
    ** Master
    */ 
    result = DEV_I2C_MasterInit( portID, portBaudRate );

    return(result);
}

/* Driver Close
*/ 
LEP_RESULT LeptonSDKEmb32OEM::LEP_I2C_MasterClose(LEP_CAMERA_PORT_DESC_T_PTR portDescriptorPtr)
{
    LEP_RESULT result = LEP_OK;

    /* Do any device-specific calls to implement a close operation
    */ 
	result = DEV_I2C_MasterClose();
    return(result);
}

/* Driver Reset
*/ 
LEP_RESULT LeptonSDKEmb32OEM::LEP_I2C_MasterReset(LEP_CAMERA_PORT_DESC_T_PTR portDescriptorPtr )
{
    LEP_RESULT result = LEP_OK;

    return(result);
}

/**
 * Driver Read
 *    Use Lepton I2C protocol for READ starting from current
 *      location
 * 
 * @param portID        User-defined parameter to identify one of multiple ports
 * 
 * @param deviceAddress This is the Lepton TWI/CCI (I2C) device address.
 * 
 * @param subAddress    Specifies the Lepton Register Address to write to
 * 
 * @param dataPtr       Pointer to the DATA buffer that is filled by this command
 * 
 * @param dataLength    Number of 16-bit words to read.
 * 
 * @return 
 */
LEP_RESULT LeptonSDKEmb32OEM::LEP_I2C_MasterReadData(LEP_UINT16 portID,
                                  LEP_UINT8  deviceAddress, 
                                  LEP_UINT16 subAddress, 
                                  LEP_UINT16 *dataPtr,
                                  LEP_UINT16 dataLength)
{
    LEP_RESULT result = LEP_OK;
    LEP_UINT16 transactionStatus;
    LEP_UINT16 numWordsRead;

    result = DEV_I2C_MasterReadData(portID,
                                    deviceAddress,
                                    subAddress,
                                    dataPtr,
                                    dataLength,
                                    &numWordsRead,
                                    &transactionStatus
                                   );

    return(result);
}

/**
 * Driver Write
 * 
 * @param portID     User-defined parameter to identify one of multiple ports
 * 
 * @param subAddress Specifies the Lepton Register Address to write to
 * 
 * @param dataPtr    Pointer to a DATA buffer to source the transfers
 * 
 * @param dataLength Specifies the number of 16-bit words to write from the bufffer
 * 
 * @return LEP_RESULT   LEP_OK if all goes well; otherwise a Lepton error code.
 */
LEP_RESULT LeptonSDKEmb32OEM::LEP_I2C_MasterWriteData(LEP_UINT16 portID,
                                   LEP_UINT8  deviceAddress, 
                                   LEP_UINT16 subAddress, 
                                   LEP_UINT16 *dataPtr,
                                   LEP_UINT16 dataLength)
{
    LEP_RESULT result = LEP_OK;
    LEP_UINT16 transactionStatus;
    LEP_UINT16 numWordsWritten;

    result = DEV_I2C_MasterWriteData(portID,
                                     deviceAddress,
                                     subAddress,
                                     dataPtr,
                                     dataLength,
                                     &numWordsWritten,
                                     &transactionStatus
                                    );
    return(result);
}


LEP_RESULT LeptonSDKEmb32OEM::LEP_I2C_MasterReadRegister(LEP_UINT16 portID,
                                      LEP_UINT8  deviceAddress, 
                                      LEP_UINT16 regAddress,
                                      LEP_UINT16 *regValue)
{
    LEP_RESULT result = LEP_OK;
    LEP_UINT16 transactionStatus;

    result = DEV_I2C_MasterReadRegister(portID,
                                        deviceAddress,
                                        regAddress,
                                        regValue,
                                        &transactionStatus
                                       );
    return(result);
}


LEP_RESULT LeptonSDKEmb32OEM::LEP_I2C_MasterWriteRegister(LEP_UINT16 portID,
                                       LEP_UINT8  deviceAddress, 
                                       LEP_UINT16 regAddress,
                                       LEP_UINT16 regValue)
{
    LEP_RESULT result = LEP_OK;
    LEP_UINT16 transactionStatus;

    result = DEV_I2C_MasterWriteRegister(portID,
                                         deviceAddress,
                                         regAddress,
                                         regValue,
                                         &transactionStatus
                                        );
    return(result);
}


/* Driver Status
*/ 
LEP_RESULT LeptonSDKEmb32OEM::LEP_I2C_MasterStatus(LEP_UINT16 portID,
                                LEP_UINT16 *portStatus )
{
    LEP_RESULT result = LEP_OK;

    return(result);
}


/**************************************/
/*                OEM                 */
/**************************************/
/******************************************************************************/
/**
 * Power Down the Camera by asserting the POWERDOWN condition.
 * 
 * @param portDescPtr
 * 
 * @return 
 */
LEP_RESULT LeptonSDKEmb32OEM::LEP_RunOemPowerDown( LEP_CAMERA_PORT_DESC_T_PTR portDescPtr )
{
   LEP_RESULT  result = LEP_OK;

   result = LEP_RunCommand( portDescPtr, ( LEP_COMMAND_ID )LEP_CID_OEM_POWER_DOWN );

   return( result );
}

LEP_RESULT LeptonSDKEmb32OEM::LEP_RunOemPowerOn( LEP_CAMERA_PORT_DESC_T_PTR portDescPtr )
{
   LEP_RESULT result = LEP_OK;

   result = LEP_DirectWriteRegister( portDescPtr, 0x0, 0x0 );

   return( result );
}

/**
 * Places the Camera into the Stand By condition.
 * 
 * @param portDescPtr
 * 
 * @return 
 */
LEP_RESULT LeptonSDKEmb32OEM::LEP_RunOemStandby( LEP_CAMERA_PORT_DESC_T_PTR portDescPtr )
{
   LEP_RESULT  result = LEP_OK;


   //result= LEP_RunCommand( portDescPtr, (LEP_COMMAND_ID)LEP_CID_OEM_STANDBY );

   return( result );
}

LEP_RESULT LeptonSDKEmb32OEM::LEP_RunOemReboot( LEP_CAMERA_PORT_DESC_T_PTR portDescPtr )
{
   LEP_RESULT result = LEP_OK;

   result = LEP_RunCommand( portDescPtr, ( LEP_COMMAND_ID )LEP_CID_OEM_REBOOT );

   return( result );
}

LEP_RESULT LeptonSDKEmb32OEM::LEP_RunOemLowPowerMode1( LEP_CAMERA_PORT_DESC_T_PTR portDescPtr )
{
   LEP_RESULT  result = LEP_OK;

   result = LEP_RunCommand( portDescPtr, ( LEP_COMMAND_ID )LEP_CID_OEM_LOW_POWER_MODE_1 );

   return( result );
}

LEP_RESULT LeptonSDKEmb32OEM::LEP_RunOemLowPowerMode2( LEP_CAMERA_PORT_DESC_T_PTR portDescPtr )
{
   LEP_RESULT  result = LEP_OK;

   result = LEP_RunCommand( portDescPtr, ( LEP_COMMAND_ID )LEP_CID_OEM_LOW_POWER_MODE_2 );

   return( result );
}

LEP_RESULT LeptonSDKEmb32OEM::LEP_RunOemBit( LEP_CAMERA_PORT_DESC_T_PTR portDescPtr )
{
   LEP_RESULT  result = LEP_OK;

   result = LEP_RunCommand( portDescPtr, ( LEP_COMMAND_ID )LEP_CID_OEM_BIT_TEST );

   return( result );
}

LEP_RESULT LeptonSDKEmb32OEM::LEP_GetOemMaskRevision( LEP_CAMERA_PORT_DESC_T_PTR portDescPtr,
                                   LEP_OEM_MASK_REVISION_T_PTR oemMaskRevisionPtr )
{
   LEP_RESULT  result = LEP_OK;
   LEP_UINT16 attributeWordLength = 1; /* one 16-bit value */

   /* Validate Parameter(s)
   */
   if( oemMaskRevisionPtr == NULL )
   {
      return( LEP_BAD_ARG_POINTER_ERROR );
   }

   /* Perform Command
   ** Reading the Camera's Chip Mask Revision
   */
   result = LEP_GetAttribute( portDescPtr,
                              ( LEP_COMMAND_ID )LEP_CID_OEM_MASK_REVISION,
                              ( LEP_ATTRIBUTE_T_PTR )oemMaskRevisionPtr,
                              attributeWordLength );
   return( result );
}
#if 0
LEP_RESULT LeptonSDKEmb32OEM::LEP_GetOemMasterID( LEP_CAMERA_PORT_DESC_T_PTR portDescPtr,
                              LEP_OEM_MASTER_ID_T_PTR oemMasterIDPtr )
{
   LEP_RESULT  result = LEP_OK;
   LEP_UINT16 attributeWordLength = 48; /* 96 bytes  */

   /* Validate Parameter(s)
   */
   if( oemMasterIDPtr == NULL )
   {
      return( LEP_BAD_ARG_POINTER_ERROR );
   }

   /* Perform Command
   ** Reading the Camera's Chip Master ID
   */
   result = LEP_GetAttribute( portDescPtr,
                             ( LEP_COMMAND_ID )LEP_CID_OEM_MASTER_ID,
                             ( LEP_ATTRIBUTE_T_PTR )oemMasterIDPtr,
                             attributeWordLength );
   return( result );
}
#endif

#if USE_DEPRECATED_PART_NUMBER_INTERFACE
LEP_RESULT LeptonSDKEmb32OEM::LEP_GetOemFlirPartNumber( LEP_CAMERA_PORT_DESC_T_PTR portDescPtr,
                                     LEP_OEM_PART_NUMBER_T_PTR oemPartNumberPtr )
{
   LEP_RESULT  result = LEP_OK;
   LEP_UINT16 attributeWordLength = 16; /* 32 bytes */

   /* Validate Parameter(s)
   */
   if( oemPartNumberPtr == NULL )
   {
      return( LEP_BAD_ARG_POINTER_ERROR );
   }

   /* Perform Command
   ** Reading the Camera's Part Number
   */
   result = LEP_GetAttribute( portDescPtr,
                              ( LEP_COMMAND_ID )LEP_CID_OEM_FLIR_PART_NUMBER,
                              ( LEP_ATTRIBUTE_T_PTR )oemPartNumberPtr,
                              attributeWordLength );

   return( result );
}

LEP_RESULT LeptonSDKEmb32OEM::LEP_GetOemCustPartNumber( LEP_CAMERA_PORT_DESC_T_PTR portDescPtr,
                                     LEP_OEM_PART_NUMBER_T_PTR oemPartNumberPtr )
{
   LEP_RESULT result = LEP_OK;
   LEP_UINT16 attributeWordLength = 16;   /* 32 bytes */

   if( oemPartNumberPtr == NULL )
   {
      return( LEP_BAD_ARG_POINTER_ERROR );
   }

   result = LEP_GetAttribute( portDescPtr,
                              ( LEP_COMMAND_ID )LEP_CID_OEM_CUST_PART_NUMBER,
                              ( LEP_ATTRIBUTE_T_PTR )oemPartNumberPtr,
                              attributeWordLength );

   return( result );
}
#else
LEP_RESULT LeptonSDKEmb32OEM::LEP_GetOemFlirPartNumber( LEP_CAMERA_PORT_DESC_T_PTR portDescPtr,
                                     LEP_OEM_PART_NUMBER_T_PTR oemPartNumberPtr )
{
   LEP_RESULT result = LEP_OK;
   LEP_UINT16 attributeWordLength = 16; /* 32 bytes */

   /* Validate Parameter(s)
   */
   if( oemPartNumberPtr == NULL )
   {
      return( LEP_BAD_ARG_POINTER_ERROR );
   }

   /* Perform Command
   ** Reading the Camera's Part Number
   */
   result = LEP_GetAttribute( portDescPtr,
                              ( LEP_COMMAND_ID )LEP_CID_OEM_FLIR_PART_NUMBER,
                              ( LEP_ATTRIBUTE_T_PTR )oemPartNumberPtr,
                              attributeWordLength );

   return( result );
}
LEP_RESULT LeptonSDKEmb32OEM::LEP_GetOemCustPartNumber( LEP_CAMERA_PORT_DESC_T_PTR portDescPtr,
                                     LEP_OEM_PART_NUMBER_T_PTR oemPartNumberPtr )
{
   LEP_RESULT result = LEP_OK;
   LEP_UINT16 attributeWordLength = 16;   /* 32 bytes */

   if( oemPartNumberPtr == NULL )
   {
      return( LEP_BAD_ARG_POINTER_ERROR );
   }

   result = LEP_GetAttribute( portDescPtr,
                              ( LEP_COMMAND_ID )LEP_CID_OEM_CUST_PART_NUMBER,
                              ( LEP_ATTRIBUTE_T_PTR )oemPartNumberPtr,
                              attributeWordLength );


   return( result );
}
#endif

LEP_RESULT LeptonSDKEmb32OEM::LEP_GetOemSoftwareVersion( LEP_CAMERA_PORT_DESC_T_PTR portDescPtr,
                                      LEP_OEM_SW_VERSION_T *oemSoftwareVersionPtr )
{
   LEP_RESULT  result = LEP_OK;
   LEP_UINT16 attributeWordLength = 4; /* 4 16-bit words to contain 64-bits */

   /* Validate Parameter(s)
   */
   if( oemSoftwareVersionPtr == NULL )
   {
      return( LEP_BAD_ARG_POINTER_ERROR );
   }

   /* Perform Command
   ** Reading the Camera's Software Version
   */
   result = LEP_GetAttribute( portDescPtr,
                              ( LEP_COMMAND_ID )LEP_CID_OEM_SOFTWARE_VERSION,
                              ( LEP_ATTRIBUTE_T_PTR )oemSoftwareVersionPtr,
                              attributeWordLength );
   return( result );
}


#if 0
LEP_RESULT LeptonSDKEmb32OEM::LEP_GetOemVendorID(LEP_CAMERA_PORT_DESC_T_PTR portDescPtr,
                              LEP_OEM_VENDORID_T *oemVendorIDPtr)
{
   LEP_RESULT  result = LEP_OK;

   return( result );
}
#endif



LEP_RESULT LeptonSDKEmb32OEM::LEP_GetOemVideoOutputEnable( LEP_CAMERA_PORT_DESC_T_PTR portDescPtr,
                                        LEP_OEM_VIDEO_OUTPUT_ENABLE_E_PTR oemVideoOutputEnablePtr )
{
   LEP_RESULT  result = LEP_OK;
   LEP_UINT16 attributeWordLength = 2; /* two 16-bit values for 32-bit enum */

   /* Validate Parameter(s)
   */
   if( oemVideoOutputEnablePtr == NULL )
   {
      return( LEP_BAD_ARG_POINTER_ERROR );
   }

   /* Perform Command
   ** Reading the Camera's current video output enable state
   */
   result = LEP_GetAttribute( portDescPtr,
                              ( LEP_COMMAND_ID )LEP_CID_OEM_VIDEO_OUTPUT_ENABLE,
                              ( LEP_ATTRIBUTE_T_PTR )oemVideoOutputEnablePtr,
                              attributeWordLength );
   return( result );
}


LEP_RESULT LeptonSDKEmb32OEM::LEP_SetOemVideoOutputEnable( LEP_CAMERA_PORT_DESC_T_PTR portDescPtr,
                                        LEP_OEM_VIDEO_OUTPUT_ENABLE_E oemVideoOutputEnable )
{
   LEP_RESULT  result = LEP_OK;
   LEP_UINT16 attributeWordLength = 2; /* two 16-bit values for 32-bit enum */

   _LEP_data[1] = 0;
   _LEP_data[0] = (LEP_UINT16) oemVideoOutputEnable;

   /* Validate Parameter(s)
   */
   if( oemVideoOutputEnable >= LEP_END_VIDEO_OUTPUT_ENABLE )
   {
      return( LEP_RANGE_ERROR );
   }

   /* Perform Command
   ** Writing the Camera's current video output enable state
   */
   result = LEP_SetAttribute( portDescPtr,
                              ( LEP_COMMAND_ID )LEP_CID_OEM_VIDEO_OUTPUT_ENABLE,
                              ( LEP_ATTRIBUTE_T_PTR ) & _LEP_data,
                              attributeWordLength );
   return( result );
}

LEP_RESULT LeptonSDKEmb32OEM::LEP_GetOemVideoOutputFormat( LEP_CAMERA_PORT_DESC_T_PTR portDescPtr,
                                        LEP_OEM_VIDEO_OUTPUT_FORMAT_E_PTR oemVideoOutputFormatPtr )
{
   LEP_RESULT  result = LEP_OK;
   LEP_UINT16 attributeWordLength = 2; /* two 16-bit values for 32-bit enum */

   /* Validate Parameter(s)
   */
   if( oemVideoOutputFormatPtr == NULL )
   {
      return( LEP_BAD_ARG_POINTER_ERROR );
   }

   /* Perform Command
   ** Reading the Camera's current video output format
   */
   result = LEP_GetAttribute( portDescPtr,
                              ( LEP_COMMAND_ID )LEP_CID_OEM_VIDEO_OUTPUT_FORMAT,
                              ( LEP_ATTRIBUTE_T_PTR )oemVideoOutputFormatPtr,
                              attributeWordLength );
   return( result );
}


LEP_RESULT LeptonSDKEmb32OEM::LEP_SetOemVideoOutputFormat( LEP_CAMERA_PORT_DESC_T_PTR portDescPtr,
                                        LEP_OEM_VIDEO_OUTPUT_FORMAT_E oemVideoOutputFormat )
{
   LEP_RESULT  result = LEP_OK;
   LEP_UINT16 attributeWordLength = 2; /* two 16-bit values for 32-bit enum */

   _LEP_data[1] = 0;
   _LEP_data[0] = (LEP_UINT16) oemVideoOutputFormat;

   /* Validate Parameter(s)
   */
   if( oemVideoOutputFormat >= LEP_END_VIDEO_OUTPUT_FORMAT )
   {
      return( LEP_RANGE_ERROR );
   }

   /* Perform Command
   ** Writing the Camera's current video output format
   */
   result = LEP_SetAttribute( portDescPtr,
                              ( LEP_COMMAND_ID )LEP_CID_OEM_VIDEO_OUTPUT_FORMAT,
                              ( LEP_ATTRIBUTE_T_PTR ) & _LEP_data,
                              attributeWordLength );
   return( result );
}

LEP_RESULT LeptonSDKEmb32OEM::LEP_GetOemVideoOutputSource( LEP_CAMERA_PORT_DESC_T_PTR portDescPtr,
                                        LEP_OEM_VIDEO_OUTPUT_SOURCE_E_PTR oemVideoOutputSourcePtr )
{
   LEP_RESULT  result = LEP_OK;
   LEP_UINT16 attributeWordLength = 2; /* two 16-bit values for 32-bit enum */

   /* Validate Parameter(s)
   */
   if( oemVideoOutputSourcePtr == NULL )
   {
      return( LEP_BAD_ARG_POINTER_ERROR );
   }

   /* Perform Command
   ** Reading the Camera's current video output source selection
   */
   result = LEP_GetAttribute( portDescPtr,
                              ( LEP_COMMAND_ID )LEP_CID_OEM_VIDEO_OUTPUT_SOURCE,
                              ( LEP_ATTRIBUTE_T_PTR )oemVideoOutputSourcePtr,
                              attributeWordLength );
   return( result );
}


LEP_RESULT LeptonSDKEmb32OEM::LEP_SetOemVideoOutputSource( LEP_CAMERA_PORT_DESC_T_PTR portDescPtr,
                                        LEP_OEM_VIDEO_OUTPUT_SOURCE_E oemVideoOutputSource )
{
   LEP_RESULT  result = LEP_OK;
   LEP_UINT16 attributeWordLength = 2; /* two 16-bit values for 32-bit enum */

   _LEP_data[1] = 0;
   _LEP_data[0] = (LEP_UINT16) oemVideoOutputSource;

   /* Validate Parameter(s)
   */
   if( oemVideoOutputSource >= LEP_END_VIDEO_OUTPUT_SOURCE )
   {
      return( LEP_RANGE_ERROR );
   }

   /* Perform Command
   ** Writing the Camera's current video output source selection
   */
   result = LEP_SetAttribute( portDescPtr,
                              ( LEP_COMMAND_ID )LEP_CID_OEM_VIDEO_OUTPUT_SOURCE,
                              ( LEP_ATTRIBUTE_T_PTR ) & _LEP_data,
                              attributeWordLength );
   return( result );
}

LEP_RESULT LeptonSDKEmb32OEM::LEP_SetOemVideoOutputSourceConstant( LEP_CAMERA_PORT_DESC_T_PTR portDescPtr,
                                                LEP_UINT16 oemVideoOutputSourceConstant )
{
   LEP_RESULT  result = LEP_OK;
   LEP_UINT16 attributeWordLength = 1; /* 1 16-bit values for constant value */


   /* Perform Command
   ** Reading the Camera's current video output source selection
   */

   result = LEP_SetAttribute( portDescPtr,
                              ( LEP_COMMAND_ID )LEP_CID_OEM_VIDEO_OUTPUT_CONSTANT,
                              ( LEP_ATTRIBUTE_T_PTR ) & oemVideoOutputSourceConstant,
                              attributeWordLength );
   return( result );
}

LEP_RESULT LeptonSDKEmb32OEM::LEP_GetOemVideoOutputSourceConstant( LEP_CAMERA_PORT_DESC_T_PTR portDescPtr,
                                                LEP_UINT16 *oemVideoOutputSourceConstPtr )
{
   LEP_RESULT  result = LEP_OK;
   LEP_UINT16 attributeWordLength = 1; /* 1 16-bit values for constant value */

   if( oemVideoOutputSourceConstPtr == NULL )
   {
      return( LEP_BAD_ARG_POINTER_ERROR );
   }

   /* Perform Command
   ** Writing the Camera's current video output source selection
   */
   result = LEP_GetAttribute( portDescPtr,
                              ( LEP_COMMAND_ID )LEP_CID_OEM_VIDEO_OUTPUT_CONSTANT,
                              ( LEP_ATTRIBUTE_T_PTR )oemVideoOutputSourceConstPtr,
                              attributeWordLength );
   return( result );
}


LEP_RESULT LeptonSDKEmb32OEM::LEP_GetOemVideoOutputChannel( LEP_CAMERA_PORT_DESC_T_PTR portDescPtr,
                                         LEP_OEM_VIDEO_OUTPUT_CHANNEL_E_PTR oemVideoOutputChannelPtr )
{
   LEP_RESULT  result = LEP_OK;
   LEP_UINT16 attributeWordLength = 2; /* two 16-bit values for 32-bit enum */

   /* Validate Parameter(s)
   */
   if( oemVideoOutputChannelPtr == NULL )
   {
      return( LEP_BAD_ARG_POINTER_ERROR );
   }

   /* Perform Command
   ** Reading the Camera's current video output channel selection
   */
   result = LEP_GetAttribute( portDescPtr,
                              ( LEP_COMMAND_ID )LEP_CID_OEM_VIDEO_OUTPUT_CHANNEL,
                              ( LEP_ATTRIBUTE_T_PTR )oemVideoOutputChannelPtr,
                              attributeWordLength );
   return( result );
}

LEP_RESULT LeptonSDKEmb32OEM::LEP_SetOemVideoOutputChannel( LEP_CAMERA_PORT_DESC_T_PTR portDescPtr,
                                         LEP_OEM_VIDEO_OUTPUT_CHANNEL_E oemVideoOutputChannel )
{
   LEP_RESULT  result = LEP_OK;
   LEP_UINT16 attributeWordLength = 2; /* two 16-bit values for 32-bit enum */

   _LEP_data[1] = 0;
   _LEP_data[0] = (LEP_UINT16) oemVideoOutputChannel;

   /* Validate Parameter(s)
   */
   if( oemVideoOutputChannel >= LEP_END_VIDEO_OUTPUT_CHANNEL )
   {
      return( LEP_RANGE_ERROR );
   }

   /* Perform Command
   ** Writing the Camera's current video output channel selection
   */
   result = LEP_SetAttribute( portDescPtr,
                              ( LEP_COMMAND_ID )LEP_CID_OEM_VIDEO_OUTPUT_CHANNEL,
                              ( LEP_ATTRIBUTE_T_PTR ) & _LEP_data,
                              attributeWordLength );
   return( result );
}

LEP_RESULT LeptonSDKEmb32OEM::LEP_GetOemVideoGammaEnable( LEP_CAMERA_PORT_DESC_T_PTR portDescPtr,
                                       LEP_OEM_VIDEO_GAMMA_ENABLE_E_PTR oemVideoGammaEnablePtr )
{
   LEP_RESULT  result = LEP_OK;
   LEP_UINT16 attributeWordLength = 2; /* two 16-bit values for 32-bit enum */

   /* Validate Parameter(s)
   */
   if( oemVideoGammaEnablePtr == NULL )
   {
      return( LEP_BAD_ARG_POINTER_ERROR );
   }

   /* Perform Command
   ** Reading the Camera's current video gamma correction enable
   */
   result = LEP_GetAttribute( portDescPtr,
                              ( LEP_COMMAND_ID )LEP_CID_OEM_VIDEO_GAMMA_ENABLE,
                              ( LEP_ATTRIBUTE_T_PTR )oemVideoGammaEnablePtr,
                              attributeWordLength );
   return( result );
}

LEP_RESULT LeptonSDKEmb32OEM::LEP_SetOemVideoGammaEnable( LEP_CAMERA_PORT_DESC_T_PTR portDescPtr,
                                       LEP_OEM_VIDEO_GAMMA_ENABLE_E oemVideoGammaEnable )
{
   LEP_RESULT  result = LEP_OK;
   LEP_UINT16 attributeWordLength = 2; /* two 16-bit values for 32-bit enum */

   _LEP_data[1] = 0;
   _LEP_data[0] = (LEP_UINT16) oemVideoGammaEnable;

   /* Validate Parameter(s)
   */
   if( oemVideoGammaEnable >= LEP_END_VIDEO_GAMMA_ENABLE )
   {
      return( LEP_RANGE_ERROR );
   }

   /* Perform Command
   ** Writing the Camera's current video output channel selection
   */
   result = LEP_SetAttribute( portDescPtr,
                              ( LEP_COMMAND_ID )LEP_CID_OEM_VIDEO_GAMMA_ENABLE,
                              ( LEP_ATTRIBUTE_T_PTR ) & _LEP_data,
                              attributeWordLength );
   return( result );
}

LEP_RESULT LeptonSDKEmb32OEM::LEP_GetOemCalStatus( LEP_CAMERA_PORT_DESC_T_PTR portDescPtr,
                                LEP_OEM_STATUS_E_PTR calStatusPtr )
{
   LEP_RESULT  result = LEP_OK;
   LEP_UINT16 attributeWordLength = 2;

   if( calStatusPtr == NULL )
   {
      return( LEP_BAD_ARG_POINTER_ERROR );
   }

   result = LEP_GetAttribute( portDescPtr,
                              ( LEP_COMMAND_ID )LEP_CID_OEM_STATUS,
                              ( LEP_ATTRIBUTE_T_PTR )calStatusPtr,
                              attributeWordLength );

   return( result );
}

LEP_RESULT LeptonSDKEmb32OEM::LEP_GetOemFFCNormalizationTarget( LEP_CAMERA_PORT_DESC_T_PTR portDescPtr,
                                             LEP_OEM_FFC_NORMALIZATION_TARGET_T_PTR ffcTargetPtr )
{
   LEP_RESULT result = LEP_OK;
   LEP_UINT16 attributeWordLength = 1;    /* FFC Target is a single 16-bit value */

   if( ffcTargetPtr == NULL )
   {
      return( LEP_BAD_ARG_POINTER_ERROR );
   }

   result = LEP_GetAttribute( portDescPtr,
                              ( LEP_COMMAND_ID )LEP_CID_OEM_FFC_NORMALIZATION_TARGET,
                              ( LEP_ATTRIBUTE_T_PTR )ffcTargetPtr,
                              attributeWordLength );

   return( result );
}

LEP_RESULT LeptonSDKEmb32OEM::LEP_SetOemFFCNormalizationTarget( LEP_CAMERA_PORT_DESC_T_PTR portDescPtr,
                                             LEP_OEM_FFC_NORMALIZATION_TARGET_T ffcTarget )
{
   LEP_RESULT result = LEP_OK;
   LEP_UINT16 attributeWordLength = 1; /* single 16-bit value */

   result = LEP_SetAttribute( portDescPtr,
                              ( LEP_COMMAND_ID )LEP_CID_OEM_FFC_NORMALIZATION_TARGET,
                              ( LEP_ATTRIBUTE_T_PTR ) & ffcTarget,
                              attributeWordLength );

   return( result );
}

LEP_RESULT LeptonSDKEmb32OEM::LEP_RunOemFFCNormalization( LEP_CAMERA_PORT_DESC_T_PTR portDescPtr,
                                       LEP_OEM_FFC_NORMALIZATION_TARGET_T ffcTarget )
{
   LEP_RESULT result = LEP_OK;
   LEP_OEM_STATUS_E oemStatus = LEP_OEM_STATUS_BUSY;

   result = LEP_SetOemFFCNormalizationTarget( portDescPtr, ffcTarget );
   if( result == LEP_OK )
   {
      result = LEP_RunCommand( portDescPtr, ( LEP_COMMAND_ID )LEP_CID_OEM_FFC_NORMALIZATION_TARGET );
      while( oemStatus == LEP_OEM_STATUS_BUSY )
      {
         LEP_GetOemCalStatus( portDescPtr, &oemStatus );
      }
   }

   return( result );

}

LEP_RESULT LeptonSDKEmb32OEM::LEP_RunOemFFC( LEP_CAMERA_PORT_DESC_T_PTR portDescPtr )
{
   LEP_RESULT result = LEP_OK;
   LEP_OEM_STATUS_E oemStatus = LEP_OEM_STATUS_BUSY;

   result = LEP_RunCommand( portDescPtr, ( LEP_COMMAND_ID )LEP_CID_OEM_FFC_NORMALIZATION_TARGET );
   while( oemStatus == LEP_OEM_STATUS_BUSY )
   {
      LEP_GetOemCalStatus( portDescPtr, &oemStatus );
   }

   return( result );

}

LEP_RESULT LeptonSDKEmb32OEM::LEP_GetOemFrameMean( LEP_CAMERA_PORT_DESC_T_PTR portDescPtr,
                                LEP_OEM_FRAME_AVERAGE_T_PTR frameAveragePtr )
{
   LEP_RESULT  result = LEP_OK;
   LEP_UINT16 attributeWordLength = 1;

   if( frameAveragePtr == NULL )
   {
      return( LEP_BAD_ARG_POINTER_ERROR );
   }

   result = LEP_GetAttribute(  portDescPtr,
                              ( LEP_COMMAND_ID )LEP_CID_OEM_SCENE_MEAN_VALUE,
                              ( LEP_ATTRIBUTE_T_PTR )frameAveragePtr,
                              attributeWordLength );

   return( result );
}

LEP_RESULT LeptonSDKEmb32OEM::LEP_GetOemPowerMode( LEP_CAMERA_PORT_DESC_T_PTR portDescPtr,
                                LEP_OEM_POWER_STATE_E_PTR powerModePtr )
{
   LEP_RESULT result = LEP_OK;
   LEP_UINT16 attributeWordLength = 2;    /* enums are 32-bit */

   if( powerModePtr == NULL )
   {
      return( LEP_BAD_ARG_POINTER_ERROR );
   }

   result = LEP_GetAttribute( portDescPtr,
                              ( LEP_COMMAND_ID )LEP_CID_OEM_POWER_MODE,
                              ( LEP_ATTRIBUTE_T_PTR )powerModePtr,
                              attributeWordLength );

   return( result );
}

LEP_RESULT LeptonSDKEmb32OEM::LEP_SetOemPowerMode( LEP_CAMERA_PORT_DESC_T_PTR portDescPtr,
                                LEP_OEM_POWER_STATE_E powerMode )
{
   LEP_RESULT result = LEP_OK;
   LEP_UINT16 attributeWordLength = 2;    /* enums are 32-bit */

   _LEP_data[1] = 0;
   _LEP_data[0] = (LEP_UINT16) powerMode;

   if( powerMode >= LEP_OEM_END_POWER_MODE )
   {
      return( LEP_RANGE_ERROR );
   }

   result = LEP_SetAttribute( portDescPtr,
                              ( LEP_COMMAND_ID )LEP_CID_OEM_POWER_MODE,
                              ( LEP_ATTRIBUTE_T_PTR ) & _LEP_data,
                              attributeWordLength );

   return( result );
}

LEP_RESULT LeptonSDKEmb32OEM::LEP_GetOemGpioMode( LEP_CAMERA_PORT_DESC_T_PTR portDescPtr,
                               LEP_OEM_GPIO_MODE_E_PTR gpioModePtr )
{
   LEP_RESULT result = LEP_OK;
   LEP_UINT16 attributeWordLength = 2;    /* enums are 32-bit */

   if( gpioModePtr == NULL )
   {
      return( LEP_BAD_ARG_POINTER_ERROR );
   }

   result = LEP_GetAttribute( portDescPtr,
                              ( LEP_COMMAND_ID )LEP_CID_OEM_GPIO_MODE_SELECT,
                              ( LEP_ATTRIBUTE_T_PTR )gpioModePtr,
                              attributeWordLength );

   return( result );
}
LEP_RESULT LeptonSDKEmb32OEM::LEP_SetOemGpioMode( LEP_CAMERA_PORT_DESC_T_PTR portDescPtr,
                               LEP_OEM_GPIO_MODE_E gpioMode )
{
   LEP_RESULT result = LEP_OK;
   LEP_UINT16 attributeWordLength = 2;    /* enums are 32-bit */

   _LEP_data[1] = 0;
   _LEP_data[0] = (LEP_UINT16) gpioMode;

   if ( gpioMode >= LEP_OEM_END_GPIO_MODE )
   {
      return( LEP_RANGE_ERROR );
   }

   result = LEP_SetAttribute( portDescPtr,
                              ( LEP_COMMAND_ID )LEP_CID_OEM_GPIO_MODE_SELECT,
                              ( LEP_ATTRIBUTE_T_PTR ) & _LEP_data,
                              attributeWordLength );
   return( result );
}
LEP_RESULT LeptonSDKEmb32OEM::LEP_GetOemGpioVsyncPhaseDelay( LEP_CAMERA_PORT_DESC_T_PTR portDescPtr,
                                          LEP_OEM_VSYNC_DELAY_E_PTR numHsyncLinesPtr )
{
   LEP_RESULT result = LEP_OK;
   LEP_UINT16 attributeWordLength = 2;    /* enums are 32-bit */

   if( numHsyncLinesPtr == NULL )
   {
      return( LEP_BAD_ARG_POINTER_ERROR );
   }

   result = LEP_GetAttribute( portDescPtr,
                              ( LEP_COMMAND_ID )LEP_CID_OEM_GPIO_VSYNC_PHASE_DELAY,
                              ( LEP_ATTRIBUTE_T_PTR )numHsyncLinesPtr,
                              attributeWordLength );

   return( result );
}
LEP_RESULT LeptonSDKEmb32OEM::LEP_SetOemGpioVsyncPhaseDelay( LEP_CAMERA_PORT_DESC_T_PTR portDescPtr,
                                          LEP_OEM_VSYNC_DELAY_E numHsyncLines )
{
   LEP_RESULT result = LEP_OK;
   LEP_UINT16 attributeWordLength = 2;    /* enums are 32-bit */

   _LEP_data[1] = 0;
   _LEP_data[0] = (LEP_INT16) numHsyncLines;

   if( numHsyncLines >= LEP_END_OEM_VSYNC_DELAY )
   {
      return( LEP_RANGE_ERROR );
   }

   result = LEP_SetAttribute( portDescPtr,
                              ( LEP_COMMAND_ID )LEP_CID_OEM_GPIO_VSYNC_PHASE_DELAY,
                              ( LEP_ATTRIBUTE_T_PTR ) & _LEP_data,
                              attributeWordLength );

   return( result );
}

LEP_RESULT LeptonSDKEmb32OEM::LEP_GetOemUserDefaultsState( LEP_CAMERA_PORT_DESC_T_PTR portDescPtr,
                                        LEP_OEM_USER_PARAMS_STATE_E_PTR userParamsStatePtr )
{
   LEP_RESULT result = LEP_OK;
   LEP_UINT16 attributeWordLength = 2;    /* enums are 32-bit */

   if( userParamsStatePtr == NULL )
   {
      return( LEP_BAD_ARG_POINTER_ERROR );
   }

   result = LEP_GetAttribute( portDescPtr,
                              ( LEP_COMMAND_ID )LEP_CID_OEM_USER_DEFAULTS,
                              ( LEP_ATTRIBUTE_T_PTR )userParamsStatePtr,
                              attributeWordLength );

   return( result );
}

LEP_RESULT LeptonSDKEmb32OEM::LEP_RunOemUserDefaultsCopyToOtp( LEP_CAMERA_PORT_DESC_T_PTR portDescPtr )
{
   LEP_RESULT result = LEP_OK;

   result = LEP_RunCommand( portDescPtr, ( LEP_COMMAND_ID )LEP_CID_OEM_USER_DEFAULTS );

   return( result );
}

LEP_RESULT LeptonSDKEmb32OEM::LEP_RunOemUserDefaultsRestore( LEP_CAMERA_PORT_DESC_T_PTR portDescPtr )
{
   LEP_RESULT result = LEP_OK;

   result = LEP_RunCommand( portDescPtr, ( LEP_COMMAND_ID )LEP_CID_OEM_USER_DEFAULTS_RESTORE );

   return( result );
}



LEP_RESULT LeptonSDKEmb32OEM::LEP_SetOemThermalShutdownEnable( LEP_CAMERA_PORT_DESC_T_PTR portDescPtr,
                                            LEP_OEM_THERMAL_SHUTDOWN_ENABLE_T ThermalShutdownEnableState )
{
   LEP_RESULT result = LEP_OK;
   LEP_UINT16 attributeWordLength = 2; /* one enum = two words */

   _LEP_data[1] = 0;
   _LEP_data[0] = (LEP_UINT16) ThermalShutdownEnableState.oemThermalShutdownEnable;

   if( ThermalShutdownEnableState.oemThermalShutdownEnable >= LEP_OEM_END_STATE )
   {
      return( LEP_RANGE_ERROR );
   }
   /* Perform Command
   ** Writing the Camera's current video freeze enable state
   */
   result = LEP_SetAttribute( portDescPtr,
                              ( LEP_COMMAND_ID )LEP_CID_OEM_THERMAL_SHUTDOWN_ENABLE_STATE,
                              ( LEP_ATTRIBUTE_T_PTR ) & _LEP_data,
                              attributeWordLength );
   return( result );
}

LEP_RESULT LeptonSDKEmb32OEM::LEP_GetOemThermalShutdownEnable( LEP_CAMERA_PORT_DESC_T_PTR portDescPtr,
                                            LEP_OEM_THERMAL_SHUTDOWN_ENABLE_T_PTR ThermalShutdownEnableStatePtr )
{
   LEP_RESULT result = LEP_OK;
   LEP_UINT16 attributeWordLength = 2; /* one enum = two words */

   if( ThermalShutdownEnableStatePtr == NULL )
   {
      return( LEP_BAD_ARG_POINTER_ERROR );
   }
   result = LEP_GetAttribute( portDescPtr,
                              ( LEP_COMMAND_ID )LEP_CID_OEM_THERMAL_SHUTDOWN_ENABLE_STATE,
                              ( LEP_ATTRIBUTE_T_PTR )ThermalShutdownEnableStatePtr,
                              attributeWordLength );
   return( result );
}

LEP_RESULT LeptonSDKEmb32OEM::LEP_SetOemShutterProfileObj( LEP_CAMERA_PORT_DESC_T_PTR portDescPtr,
                                        LEP_OEM_SHUTTER_PROFILE_OBJ_T ShutterProfileObj )
{
   LEP_RESULT result = LEP_OK;
   LEP_UINT16 attributeWordLength = 2; /* 2 words */

   _LEP_data[1] = ShutterProfileObj.openPeriodInFrames;
   _LEP_data[0] = ShutterProfileObj.closePeriodInFrames;

   /* Perform Command
   ** Writing the Camera's current video freeze enable state
   */
   result = LEP_SetAttribute( portDescPtr,
                              ( LEP_COMMAND_ID )LEP_CID_OEM_SHUTTER_PROFILE_OBJ,
                              ( LEP_ATTRIBUTE_T_PTR ) & _LEP_data,
                              attributeWordLength );
   return( result );
}

LEP_RESULT LeptonSDKEmb32OEM::LEP_GetOemShutterProfileObj( LEP_CAMERA_PORT_DESC_T_PTR portDescPtr,
                                        LEP_OEM_SHUTTER_PROFILE_OBJ_T_PTR ShutterProfileObjPtr )
{
   LEP_RESULT result = LEP_OK;
   LEP_UINT16 attributeWordLength = 2; /* 2 words */

   if( ShutterProfileObjPtr == NULL )
   {
      return( LEP_BAD_ARG_POINTER_ERROR );
   }
   result = LEP_GetAttribute( portDescPtr,
                              ( LEP_COMMAND_ID )LEP_CID_OEM_SHUTTER_PROFILE_OBJ,
                              ( LEP_ATTRIBUTE_T_PTR )ShutterProfileObjPtr,
                              attributeWordLength );
   return( result );
}


LEP_RESULT LeptonSDKEmb32OEM::LEP_SetOemBadPixelReplaceControl( LEP_CAMERA_PORT_DESC_T_PTR portDescPtr,
                                             LEP_OEM_BAD_PIXEL_REPLACE_CONTROL_T BadPixelReplaceControl )
{
   LEP_RESULT result = LEP_OK;
   LEP_UINT16 attributeWordLength = 2; /* two word enums */

   _LEP_data[1] = 0;
   _LEP_data[0] = (LEP_UINT16) BadPixelReplaceControl.oemBadPixelReplaceEnable;

   /* Perform Command
   ** Writing the Camera's current video freeze enable state
   */
   result = LEP_SetAttribute( portDescPtr,
                              ( LEP_COMMAND_ID )LEP_CID_OEM_BAD_PIXEL_REPLACE_CONTROL,
                              ( LEP_ATTRIBUTE_T_PTR ) & _LEP_data,
                              attributeWordLength );

   return( result );
}

LEP_RESULT LeptonSDKEmb32OEM::LEP_GetOemBadPixelReplaceControl( LEP_CAMERA_PORT_DESC_T_PTR portDescPtr,
                                             LEP_OEM_BAD_PIXEL_REPLACE_CONTROL_T_PTR BadPixelReplaceControlPtr )
{
   LEP_RESULT result = LEP_OK;
   LEP_UINT16 attributeWordLength = 2; /* one enum */
   if( BadPixelReplaceControlPtr == NULL )
   {
      return( LEP_BAD_ARG_POINTER_ERROR );
   }
   result = LEP_GetAttribute( portDescPtr,
                              ( LEP_COMMAND_ID )LEP_CID_OEM_BAD_PIXEL_REPLACE_CONTROL,
                              ( LEP_ATTRIBUTE_T_PTR )BadPixelReplaceControlPtr,
                              attributeWordLength );
   return( result );
}

LEP_RESULT LeptonSDKEmb32OEM::LEP_SetOemTemporalFilterControl( LEP_CAMERA_PORT_DESC_T_PTR portDescPtr,
                                            LEP_OEM_TEMPORAL_FILTER_CONTROL_T TemporalFilterControl )
{
   LEP_RESULT result = LEP_OK;
   LEP_UINT16 attributeWordLength = 2; /* one enum = two words */

   _LEP_data[1] = 0;
   _LEP_data[0] = (LEP_UINT16) TemporalFilterControl.oemTemporalFilterEnable;;

   /* Perform Command
   ** Writing the Camera's current video freeze enable state
   */
   result = LEP_SetAttribute( portDescPtr,
                              ( LEP_COMMAND_ID )LEP_CID_OEM_TEMPORAL_FILTER_CONTROL,
                              ( LEP_ATTRIBUTE_T_PTR ) & _LEP_data,
                              attributeWordLength );
   return( result );
}

LEP_RESULT LeptonSDKEmb32OEM::LEP_GetOemTemporalFilterControl( LEP_CAMERA_PORT_DESC_T_PTR portDescPtr,
                                            LEP_OEM_TEMPORAL_FILTER_CONTROL_T_PTR TemporalFilterControlPtr )
{
   LEP_RESULT result = LEP_OK;
   LEP_UINT16 attributeWordLength = 2; /* one enum = two words */
   if( TemporalFilterControlPtr == NULL )
   {
      return( LEP_BAD_ARG_POINTER_ERROR );
   }
   result = LEP_GetAttribute( portDescPtr,
                              ( LEP_COMMAND_ID )LEP_CID_OEM_TEMPORAL_FILTER_CONTROL,
                              ( LEP_ATTRIBUTE_T_PTR )TemporalFilterControlPtr,
                              attributeWordLength );
   return( result );
}

LEP_RESULT LeptonSDKEmb32OEM::LEP_SetOemColumnNoiseEstimateControl( LEP_CAMERA_PORT_DESC_T_PTR portDescPtr,
                                                 LEP_OEM_COLUMN_NOISE_ESTIMATE_CONTROL_T ColumnNoiseEstimateControl )
{
   LEP_RESULT result = LEP_OK;
   LEP_UINT16 attributeWordLength = 2; /* one enum = two words */

   _LEP_data[1] = 0;
   _LEP_data[0] = (LEP_UINT16) ColumnNoiseEstimateControl.oemColumnNoiseEstimateEnable;;

   result = LEP_SetAttribute( portDescPtr,
                              ( LEP_COMMAND_ID )LEP_CID_OEM_COLUMN_NOISE_ESTIMATE_CONTROL,
                              ( LEP_ATTRIBUTE_T_PTR ) & _LEP_data,
                              attributeWordLength );
   return( result );
}

LEP_RESULT LeptonSDKEmb32OEM::LEP_GetOemColumnNoiseEstimateControl( LEP_CAMERA_PORT_DESC_T_PTR portDescPtr,
                                                 LEP_OEM_COLUMN_NOISE_ESTIMATE_CONTROL_T_PTR ColumnNoiseEstimateControlPtr )
{
   LEP_RESULT result = LEP_OK;
   LEP_UINT16 attributeWordLength = 2; /* one enum = two words */
   if( ColumnNoiseEstimateControlPtr == NULL )
   {
      return( LEP_BAD_ARG_POINTER_ERROR );
   }
   result = LEP_GetAttribute( portDescPtr,
                              ( LEP_COMMAND_ID )LEP_CID_OEM_COLUMN_NOISE_ESTIMATE_CONTROL,
                              ( LEP_ATTRIBUTE_T_PTR )ColumnNoiseEstimateControlPtr,
                              attributeWordLength );
   return( result );
}

LEP_RESULT LeptonSDKEmb32OEM::LEP_GetOemPixelNoiseSettings( LEP_CAMERA_PORT_DESC_T_PTR portDescPtr,
                                         LEP_OEM_PIXEL_NOISE_SETTINGS_T_PTR pixelNoiseSettingsPtr )
{
   LEP_RESULT result = LEP_OK;
   LEP_UINT16 attributeWordLength = 2;    /* struct size 4 bytes */

   if( pixelNoiseSettingsPtr == NULL )
   {
      return( LEP_BAD_ARG_POINTER_ERROR );
   }

   result = LEP_GetAttribute( portDescPtr,
                              ( LEP_COMMAND_ID )LEP_CID_OEM_PIXEL_NOISE_ESTIMATE_CONTROL,
                              ( LEP_ATTRIBUTE_T_PTR )pixelNoiseSettingsPtr,
                              attributeWordLength );

   return( result );
}
LEP_RESULT LeptonSDKEmb32OEM::LEP_SetOemPixelNoiseSettings( LEP_CAMERA_PORT_DESC_T_PTR portDescPtr,
                                         LEP_OEM_PIXEL_NOISE_SETTINGS_T pixelNoiseSettings )
{
   LEP_RESULT result = LEP_OK;
   LEP_UINT16 attributeWordLength = 2;    /* struct size 4 bytes */

   _LEP_data[1] = 0;
   _LEP_data[0] = (LEP_UINT16) pixelNoiseSettings.oemPixelNoiseEstimateEnable;

   result = LEP_SetAttribute( portDescPtr,
                              ( LEP_COMMAND_ID )LEP_CID_OEM_PIXEL_NOISE_ESTIMATE_CONTROL,
                              ( LEP_ATTRIBUTE_T_PTR ) & _LEP_data,
                              attributeWordLength );

   return( result );
}


/**************************************/
/*                RAD                 */
/**************************************/
LEP_RESULT LeptonSDKEmb32OEM::LEP_GetRadTShutterMode( LEP_CAMERA_PORT_DESC_T_PTR portDescPtr,
                                   LEP_RAD_TS_MODE_E_PTR radTShutterModePtr )
{
   LEP_RESULT result = LEP_OK;
   LEP_UINT16 attributeWordLength = 2; /* two 16-bit values for 32-bit enum */

   /* Validate Parameter(s)
   */
   if( radTShutterModePtr == NULL )
   {
      return( LEP_BAD_ARG_POINTER_ERROR );
   }

   /* Perform Command
   ** Reading the Camera's current TShutter mode
   */
   result = LEP_GetAttribute( portDescPtr,
                              ( LEP_COMMAND_ID )LEP_CID_RAD_TSHUTTER_MODE,
                              ( LEP_ATTRIBUTE_T_PTR )radTShutterModePtr,
                              attributeWordLength );
   return( result );
}

LEP_RESULT LeptonSDKEmb32OEM::LEP_SetRadTShutterMode( LEP_CAMERA_PORT_DESC_T_PTR portDescPtr,
                                   LEP_RAD_TS_MODE_E radTShutterMode )
{
   LEP_RESULT result = LEP_OK;
   LEP_UINT16 attributeWordLength = 2; /* two 16-bit values for 32-bit enum */

   _LEP_data[1] = 0;
   _LEP_data[0] = (LEP_UINT16) radTShutterMode;

   /* Validate Parameter(s)
   */
   if( radTShutterMode >= LEP_RAD_TS_END_TS_MODE )
   {
      return( LEP_RANGE_ERROR );
   }

   /* Perform Command
   ** Writing the Camera's current TShutter mode
   */
   result = LEP_SetAttribute( portDescPtr,
                              ( LEP_COMMAND_ID )LEP_CID_RAD_TSHUTTER_MODE,
                              ( LEP_ATTRIBUTE_T_PTR ) & _LEP_data,
                              attributeWordLength );
   return( result );
}


LEP_RESULT LeptonSDKEmb32OEM::LEP_GetRadTShutter( LEP_CAMERA_PORT_DESC_T_PTR portDescPtr,
                               LEP_RAD_KELVIN_T_PTR radTShutterPtr )
{
   LEP_RESULT result = LEP_OK;
   LEP_UINT16 attributeWordLength = 1;    // single 16-bit word

   if( radTShutterPtr == NULL )
   {
      return( LEP_BAD_ARG_POINTER_ERROR );
   }
   result = LEP_GetAttribute(  portDescPtr,
                              ( LEP_COMMAND_ID )LEP_CID_RAD_TSHUTTER,
                              ( LEP_ATTRIBUTE_T_PTR )radTShutterPtr,
                              attributeWordLength );
   return( result );
}

LEP_RESULT LeptonSDKEmb32OEM::LEP_SetRadTShutter( LEP_CAMERA_PORT_DESC_T_PTR portDescPtr,
                               LEP_RAD_KELVIN_T radTShutter )
{
   LEP_RESULT result = LEP_OK;
   LEP_UINT16 attributeWordLength = 1; /* single 16-bit value */

   result = LEP_SetAttribute( portDescPtr,
                              ( LEP_COMMAND_ID )LEP_CID_RAD_TSHUTTER,
                              ( LEP_ATTRIBUTE_T_PTR ) & radTShutter,
                              attributeWordLength );
   return( result );
}


LEP_RESULT LeptonSDKEmb32OEM::LEP_RunRadFFC( LEP_CAMERA_PORT_DESC_T_PTR portDescPtr )
{
   LEP_RESULT result = LEP_OK;
   LEP_RAD_STATUS_E radStatus = LEP_RAD_STATUS_BUSY;

   result = LEP_RunCommand( portDescPtr, ( LEP_COMMAND_ID )LEP_CID_RAD_RUN_FFC );
   if( result == LEP_OK )
   {
      //TODO: Add timeout check
      while( radStatus == LEP_RAD_STATUS_BUSY )
      {
         LEP_GetRadRunStatus( portDescPtr, &radStatus );
      }
   }
   return( result );
}


LEP_RESULT LeptonSDKEmb32OEM::LEP_GetRadRBFOInternal0( LEP_CAMERA_PORT_DESC_T_PTR portDescPtr,
                                    LEP_RBFO_T_PTR radRBFOPtr )
{
   LEP_RESULT result = LEP_OK;
   LEP_UINT16 attributeWordLength = 8;    // RBFO is 8 16-bit words

   if( radRBFOPtr == NULL )
   {
      return( LEP_BAD_ARG_POINTER_ERROR );
   }
   result = LEP_GetAttribute(  portDescPtr,
                              ( LEP_COMMAND_ID )LEP_CID_RAD_RBFO_INTERNAL,
                              ( LEP_ATTRIBUTE_T_PTR )radRBFOPtr,
                              attributeWordLength );

   return( result );
}


LEP_RESULT LeptonSDKEmb32OEM::LEP_SetRadRBFOInternal0( LEP_CAMERA_PORT_DESC_T_PTR portDescPtr,
                                    LEP_RBFO_T_PTR radRBFOPtr )
{
   LEP_RESULT result = LEP_OK;
   LEP_UINT16 attributeWordLength = 8;    // RBFO is 8 16-bit words

   _LEP_data[7] = (LEP_UINT16) radRBFOPtr->RBFO_O >> 16;
   _LEP_data[6] = (LEP_UINT16) radRBFOPtr->RBFO_O & 0xFFFF;
   _LEP_data[5] = (LEP_UINT16) radRBFOPtr->RBFO_F >> 16;
   _LEP_data[4] = (LEP_UINT16) radRBFOPtr->RBFO_F & 0xFFFF;
   _LEP_data[3] = (LEP_UINT16) radRBFOPtr->RBFO_B >> 16;
   _LEP_data[2] = (LEP_UINT16) radRBFOPtr->RBFO_B & 0xFFFF;
   _LEP_data[1] = (LEP_UINT16) radRBFOPtr->RBFO_R >> 16;
   _LEP_data[0] = (LEP_UINT16) radRBFOPtr->RBFO_R & 0xFFFF;

   if( radRBFOPtr == NULL )
   {
      return( LEP_BAD_ARG_POINTER_ERROR );
   }
   result = LEP_SetAttribute( portDescPtr,
                              ( LEP_COMMAND_ID )LEP_CID_RAD_RBFO_INTERNAL,
                              ( LEP_ATTRIBUTE_T_PTR ) & _LEP_data,
                              attributeWordLength );

   return( result );
}


LEP_RESULT LeptonSDKEmb32OEM::LEP_GetRadRBFOExternal0( LEP_CAMERA_PORT_DESC_T_PTR portDescPtr,
                                    LEP_RBFO_T_PTR radRBFOPtr )
{
   LEP_RESULT result = LEP_OK;
   LEP_UINT16 attributeWordLength = 8;    // RBFO is 8 16-bit words

   if( radRBFOPtr == NULL )
   {
      return( LEP_BAD_ARG_POINTER_ERROR );
   }
   result = LEP_GetAttribute(  portDescPtr,
                              ( LEP_COMMAND_ID )LEP_CID_RAD_RBFO_EXTERNAL,
                              ( LEP_ATTRIBUTE_T_PTR )radRBFOPtr,
                              attributeWordLength );

   return( result );
}


LEP_RESULT LeptonSDKEmb32OEM::LEP_SetRadRBFOExternal0( LEP_CAMERA_PORT_DESC_T_PTR portDescPtr,
                                    LEP_RBFO_T_PTR radRBFOPtr )
{
   LEP_RESULT result = LEP_OK;
   LEP_UINT16 attributeWordLength = 8;    // RBFO is 4 16-bit words

   _LEP_data[7] = (LEP_UINT16) radRBFOPtr->RBFO_O >> 16;
   _LEP_data[6] = (LEP_UINT16) radRBFOPtr->RBFO_O & 0xFFFF;
   _LEP_data[5] = (LEP_UINT16) radRBFOPtr->RBFO_F >> 16;
   _LEP_data[4] = (LEP_UINT16) radRBFOPtr->RBFO_F & 0xFFFF;
   _LEP_data[3] = (LEP_UINT16) radRBFOPtr->RBFO_B >> 16;
   _LEP_data[2] = (LEP_UINT16) radRBFOPtr->RBFO_B & 0xFFFF;
   _LEP_data[1] = (LEP_UINT16) radRBFOPtr->RBFO_R >> 16;
   _LEP_data[0] = (LEP_UINT16) radRBFOPtr->RBFO_R & 0xFFFF;

   if( radRBFOPtr == NULL )
   {
      return( LEP_BAD_ARG_POINTER_ERROR );
   }
   result = LEP_SetAttribute( portDescPtr,
                              ( LEP_COMMAND_ID )LEP_CID_RAD_RBFO_EXTERNAL,
                              ( LEP_ATTRIBUTE_T_PTR ) & _LEP_data,
                              attributeWordLength );

   return( result );
}


LEP_RESULT LeptonSDKEmb32OEM::LEP_GetRadInternalRBFOHighGain( LEP_CAMERA_PORT_DESC_T_PTR portDescPtr,
                                           LEP_RBFO_T_PTR radRBFOPtr )
{
   LEP_RESULT result = LEP_OK;
   LEP_UINT16 attributeWordLength = 8;    // RBFO is 8 16-bit words

   if( radRBFOPtr == NULL )
   {
      return( LEP_BAD_ARG_POINTER_ERROR );
   }
   result = LEP_GetAttribute(  portDescPtr,
                              ( LEP_COMMAND_ID )LEP_CID_RAD_RBFO_INTERNAL,
                              ( LEP_ATTRIBUTE_T_PTR )radRBFOPtr,
                              attributeWordLength );

   return( result );
}


LEP_RESULT LeptonSDKEmb32OEM::LEP_SetRadInternalRBFOHighGain( LEP_CAMERA_PORT_DESC_T_PTR portDescPtr,
                                           LEP_RBFO_T_PTR radRBFOPtr )
{
   LEP_RESULT result = LEP_OK;
   LEP_UINT16 attributeWordLength = 8;    // RBFO is 8 16-bit words

   _LEP_data[7] = (LEP_UINT16) radRBFOPtr->RBFO_O >> 16;
   _LEP_data[6] = (LEP_UINT16) radRBFOPtr->RBFO_O & 0xFFFF;
   _LEP_data[5] = (LEP_UINT16) radRBFOPtr->RBFO_F >> 16;
   _LEP_data[4] = (LEP_UINT16) radRBFOPtr->RBFO_F & 0xFFFF;
   _LEP_data[3] = (LEP_UINT16) radRBFOPtr->RBFO_B >> 16;
   _LEP_data[2] = (LEP_UINT16) radRBFOPtr->RBFO_B & 0xFFFF;
   _LEP_data[1] = (LEP_UINT16) radRBFOPtr->RBFO_R >> 16;
   _LEP_data[0] = (LEP_UINT16) radRBFOPtr->RBFO_R & 0xFFFF;

   if( radRBFOPtr == NULL )
   {
      return( LEP_BAD_ARG_POINTER_ERROR );
   }
   result = LEP_SetAttribute( portDescPtr,
                              ( LEP_COMMAND_ID )LEP_CID_RAD_RBFO_INTERNAL,
                              ( LEP_ATTRIBUTE_T_PTR ) & _LEP_data,
                              attributeWordLength );

   return( result );
}


LEP_RESULT LeptonSDKEmb32OEM::LEP_GetRadExternalRBFOHighGain( LEP_CAMERA_PORT_DESC_T_PTR portDescPtr,
                                           LEP_RBFO_T_PTR radRBFOPtr )
{
   LEP_RESULT result = LEP_OK;
   LEP_UINT16 attributeWordLength = 8;    // RBFO is 8 16-bit words

   if( radRBFOPtr == NULL )
   {
      return( LEP_BAD_ARG_POINTER_ERROR );
   }
   result = LEP_GetAttribute(  portDescPtr,
                              ( LEP_COMMAND_ID )LEP_CID_RAD_RBFO_EXTERNAL,
                              ( LEP_ATTRIBUTE_T_PTR )radRBFOPtr,
                              attributeWordLength );

   return( result );
}


LEP_RESULT LeptonSDKEmb32OEM::LEP_SetRadExternalRBFOHighGain( LEP_CAMERA_PORT_DESC_T_PTR portDescPtr,
                                           LEP_RBFO_T_PTR radRBFOPtr )
{
   LEP_RESULT result = LEP_OK;
   LEP_UINT16 attributeWordLength = 8;    // RBFO is 8 16-bit words

   _LEP_data[7] = (LEP_UINT16) radRBFOPtr->RBFO_O >> 16;
   _LEP_data[6] = (LEP_UINT16) radRBFOPtr->RBFO_O & 0xFFFF;
   _LEP_data[5] = (LEP_UINT16) radRBFOPtr->RBFO_F >> 16;
   _LEP_data[4] = (LEP_UINT16) radRBFOPtr->RBFO_F & 0xFFFF;
   _LEP_data[3] = (LEP_UINT16) radRBFOPtr->RBFO_B >> 16;
   _LEP_data[2] = (LEP_UINT16) radRBFOPtr->RBFO_B & 0xFFFF;
   _LEP_data[1] = (LEP_UINT16) radRBFOPtr->RBFO_R >> 16;
   _LEP_data[0] = (LEP_UINT16) radRBFOPtr->RBFO_R & 0xFFFF;

   if( radRBFOPtr == NULL )
   {
      return( LEP_BAD_ARG_POINTER_ERROR );
   }
   result = LEP_SetAttribute( portDescPtr,
                              ( LEP_COMMAND_ID )LEP_CID_RAD_RBFO_EXTERNAL,
                              ( LEP_ATTRIBUTE_T_PTR ) & _LEP_data,
                              attributeWordLength );

   return( result );
}


LEP_RESULT LeptonSDKEmb32OEM::LEP_GetRadInternalRBFOLowGain( LEP_CAMERA_PORT_DESC_T_PTR portDescPtr,
                                           LEP_RBFO_T_PTR radRBFOPtr )
{
   LEP_RESULT result = LEP_OK;
   LEP_UINT16 attributeWordLength = 8;    // RBFO is 8 16-bit words

   if( radRBFOPtr == NULL )
   {
      return( LEP_BAD_ARG_POINTER_ERROR );
   }
   result = LEP_GetAttribute(  portDescPtr,
                              ( LEP_COMMAND_ID )LEP_CID_RAD_RBFO_INTERNAL_LG,
                              ( LEP_ATTRIBUTE_T_PTR )radRBFOPtr,
                              attributeWordLength );

   return( result );
}


LEP_RESULT LeptonSDKEmb32OEM::LEP_SetRadInternalRBFOLowGain( LEP_CAMERA_PORT_DESC_T_PTR portDescPtr,
                                           LEP_RBFO_T_PTR radRBFOPtr )
{
   LEP_RESULT result = LEP_OK;
   LEP_UINT16 attributeWordLength = 8;    // RBFO is 8 16-bit words

   _LEP_data[7] = (LEP_UINT16) radRBFOPtr->RBFO_O >> 16;
   _LEP_data[6] = (LEP_UINT16) radRBFOPtr->RBFO_O & 0xFFFF;
   _LEP_data[5] = (LEP_UINT16) radRBFOPtr->RBFO_F >> 16;
   _LEP_data[4] = (LEP_UINT16) radRBFOPtr->RBFO_F & 0xFFFF;
   _LEP_data[3] = (LEP_UINT16) radRBFOPtr->RBFO_B >> 16;
   _LEP_data[2] = (LEP_UINT16) radRBFOPtr->RBFO_B & 0xFFFF;
   _LEP_data[1] = (LEP_UINT16) radRBFOPtr->RBFO_R >> 16;
   _LEP_data[0] = (LEP_UINT16) radRBFOPtr->RBFO_R & 0xFFFF;

   if( radRBFOPtr == NULL )
   {
      return( LEP_BAD_ARG_POINTER_ERROR );
   }
   result = LEP_SetAttribute( portDescPtr,
                              ( LEP_COMMAND_ID )LEP_CID_RAD_RBFO_INTERNAL_LG,
                              ( LEP_ATTRIBUTE_T_PTR ) & _LEP_data,
                              attributeWordLength );

   return( result );
}


LEP_RESULT LeptonSDKEmb32OEM::LEP_GetRadExternalRBFOLowGain( LEP_CAMERA_PORT_DESC_T_PTR portDescPtr,
                                           LEP_RBFO_T_PTR radRBFOPtr )
{
   LEP_RESULT result = LEP_OK;
   LEP_UINT16 attributeWordLength = 8;    // RBFO is 8 16-bit words

   if( radRBFOPtr == NULL )
   {
      return( LEP_BAD_ARG_POINTER_ERROR );
   }
   result = LEP_GetAttribute(  portDescPtr,
                              ( LEP_COMMAND_ID )LEP_CID_RAD_RBFO_EXTERNAL_LG,
                              ( LEP_ATTRIBUTE_T_PTR )radRBFOPtr,
                              attributeWordLength );

   return( result );
}


LEP_RESULT LeptonSDKEmb32OEM::LEP_SetRadExternalRBFOLowGain( LEP_CAMERA_PORT_DESC_T_PTR portDescPtr,
                                           LEP_RBFO_T_PTR radRBFOPtr )
{
   LEP_RESULT result = LEP_OK;
   LEP_UINT16 attributeWordLength = 8;    // RBFO is 4 16-bit words

   _LEP_data[7] = (LEP_UINT16) radRBFOPtr->RBFO_O >> 16;
   _LEP_data[6] = (LEP_UINT16) radRBFOPtr->RBFO_O & 0xFFFF;
   _LEP_data[5] = (LEP_UINT16) radRBFOPtr->RBFO_F >> 16;
   _LEP_data[4] = (LEP_UINT16) radRBFOPtr->RBFO_F & 0xFFFF;
   _LEP_data[3] = (LEP_UINT16) radRBFOPtr->RBFO_B >> 16;
   _LEP_data[2] = (LEP_UINT16) radRBFOPtr->RBFO_B & 0xFFFF;
   _LEP_data[1] = (LEP_UINT16) radRBFOPtr->RBFO_R >> 16;
   _LEP_data[0] = (LEP_UINT16) radRBFOPtr->RBFO_R & 0xFFFF;

   if( radRBFOPtr == NULL )
   {
      return( LEP_BAD_ARG_POINTER_ERROR );
   }
   result = LEP_SetAttribute( portDescPtr,
                              ( LEP_COMMAND_ID )LEP_CID_RAD_RBFO_EXTERNAL_LG,
                              ( LEP_ATTRIBUTE_T_PTR ) & _LEP_data,
                              attributeWordLength );

   return( result );
}

LEP_RESULT LeptonSDKEmb32OEM::LEP_GetRadResponsivityShift( LEP_CAMERA_PORT_DESC_T_PTR portDescPtr,
                                        LEP_RAD_RS_T_PTR radResponsivityShiftPtr )
{
   LEP_RESULT result = LEP_OK;
   LEP_UINT16 attributeWordLength = 1;    // single 16-bit word

   if( radResponsivityShiftPtr == NULL )
   {
      return( LEP_BAD_ARG_POINTER_ERROR );
   }
   result = LEP_GetAttribute(  portDescPtr,
                              ( LEP_COMMAND_ID )LEP_CID_RAD_RESPONSIVITY_SHIFT,
                              ( LEP_ATTRIBUTE_T_PTR )radResponsivityShiftPtr,
                              attributeWordLength );

   return( result );
}


LEP_RESULT LeptonSDKEmb32OEM::LEP_SetRadResponsivityShift( LEP_CAMERA_PORT_DESC_T_PTR portDescPtr,
                                        LEP_RAD_RS_T radResponsivityShift )
{
   LEP_RESULT result = LEP_OK;
   LEP_UINT16 attributeWordLength = 1; /* single 16-bit value */

   result = LEP_SetAttribute( portDescPtr,
                              ( LEP_COMMAND_ID )LEP_CID_RAD_RESPONSIVITY_SHIFT,
                              ( LEP_ATTRIBUTE_T_PTR ) & radResponsivityShift,
                              attributeWordLength );

   return( result );
}


LEP_RESULT LeptonSDKEmb32OEM::LEP_GetRadFNumber( LEP_CAMERA_PORT_DESC_T_PTR portDescPtr,
                              LEP_RAD_FNUMBER_T_PTR radFNumberPtr )
{
   LEP_RESULT result = LEP_OK;
   LEP_UINT16 attributeWordLength = 1;    // single 16-bit word

   if( radFNumberPtr == NULL )
   {
      return( LEP_BAD_ARG_POINTER_ERROR );
   }
   result = LEP_GetAttribute(  portDescPtr,
                              ( LEP_COMMAND_ID )LEP_CID_RAD_F_NUMBER,
                              ( LEP_ATTRIBUTE_T_PTR )radFNumberPtr,
                              attributeWordLength );

   return( result );
}


LEP_RESULT LeptonSDKEmb32OEM::LEP_SetRadFNumber( LEP_CAMERA_PORT_DESC_T_PTR portDescPtr,
                              LEP_RAD_FNUMBER_T radFNumber )
{
   LEP_RESULT result = LEP_OK;
   LEP_UINT16 attributeWordLength = 1; /* single 16-bit value */

   result = LEP_SetAttribute( portDescPtr,
                              ( LEP_COMMAND_ID )LEP_CID_RAD_F_NUMBER,
                              ( LEP_ATTRIBUTE_T_PTR ) & radFNumber,
                              attributeWordLength );

   return( result );
}


LEP_RESULT LeptonSDKEmb32OEM::LEP_GetRadTauLens( LEP_CAMERA_PORT_DESC_T_PTR portDescPtr,
                              LEP_RAD_TAULENS_T_PTR radTauLensPtr )
{
   LEP_RESULT result = LEP_OK;
   LEP_UINT16 attributeWordLength = 1;    // single 16-bit word

   if( radTauLensPtr == NULL )
   {
      return( LEP_BAD_ARG_POINTER_ERROR );
   }
   result = LEP_GetAttribute(  portDescPtr,
                              ( LEP_COMMAND_ID )LEP_CID_RAD_TAU_LENS,
                              ( LEP_ATTRIBUTE_T_PTR )radTauLensPtr,
                              attributeWordLength );

   return( result );
}


LEP_RESULT LeptonSDKEmb32OEM::LEP_SetRadTauLens( LEP_CAMERA_PORT_DESC_T_PTR portDescPtr,
                              LEP_RAD_TAULENS_T radTauLens )
{
   LEP_RESULT result = LEP_OK;
   LEP_UINT16 attributeWordLength = 1; /* single 16-bit value */

   result = LEP_SetAttribute( portDescPtr,
                              ( LEP_COMMAND_ID )LEP_CID_RAD_TAU_LENS,
                              ( LEP_ATTRIBUTE_T_PTR ) & radTauLens,
                              attributeWordLength );

   return( result );
}


LEP_RESULT LeptonSDKEmb32OEM::LEP_GetRadRadometryFilter( LEP_CAMERA_PORT_DESC_T_PTR portDescPtr,
                                      LEP_RAD_RADIOMETRY_FILTER_T_PTR radRadiometryFilterPtr )
{
   LEP_RESULT result = LEP_OK;
   LEP_UINT16 attributeWordLength = 1;    // single 16-bit word

   if( radRadiometryFilterPtr == NULL )
   {
      return( LEP_BAD_ARG_POINTER_ERROR );
   }
   result = LEP_GetAttribute(  portDescPtr,
                              ( LEP_COMMAND_ID )LEP_CID_RAD_RADIOMETRY_FILTER,
                              ( LEP_ATTRIBUTE_T_PTR )radRadiometryFilterPtr,
                              attributeWordLength );

   return( result );
}


LEP_RESULT LeptonSDKEmb32OEM::LEP_SetRadRadometryFilter( LEP_CAMERA_PORT_DESC_T_PTR portDescPtr,
                                      LEP_RAD_RADIOMETRY_FILTER_T radRadiometryFilter )
{
   LEP_RESULT result = LEP_OK;
   LEP_UINT16 attributeWordLength = 1; /* single 16-bit value */

   result = LEP_SetAttribute( portDescPtr,
                              ( LEP_COMMAND_ID )LEP_CID_RAD_RADIOMETRY_FILTER,
                              ( LEP_ATTRIBUTE_T_PTR ) & radRadiometryFilter,
                              attributeWordLength );

   return( result );
}

/* Deprecated: Use LEP_GetRadTFpaLut */
LEP_RESULT LeptonSDKEmb32OEM::LEP_GetRadTFpaCLut( LEP_CAMERA_PORT_DESC_T_PTR portDescPtr,
                               LEP_RAD_LUT256_T_PTR radTFpaCLutPtr )
{
   LEP_RESULT result = LEP_OK;
   LEP_UINT16 attributeWordLength = 256;    // 256 16-bit word LUT

   if( radTFpaCLutPtr == NULL )
   {
      return( LEP_BAD_ARG_POINTER_ERROR );
   }
   result = LEP_GetAttribute(  portDescPtr,
                              ( LEP_COMMAND_ID )LEP_CID_RAD_TFPA_LUT,
                              ( LEP_ATTRIBUTE_T_PTR )radTFpaCLutPtr,
                              attributeWordLength );

   return( result );
}

/* Deprecated: Use LEP_SetRadTFpaLut */
LEP_RESULT LeptonSDKEmb32OEM::LEP_SetRadTFpaCLut( LEP_CAMERA_PORT_DESC_T_PTR portDescPtr,
                               LEP_RAD_LUT256_T_PTR radTFpaCLutPtr )
{
   LEP_RESULT result = LEP_OK;
   LEP_UINT16 attributeWordLength = 256;    // 256 16-bit word LUT

   if( radTFpaCLutPtr == NULL )
   {
      return( LEP_BAD_ARG_POINTER_ERROR );
   }
   result = LEP_SetAttribute( portDescPtr,
                              ( LEP_COMMAND_ID )LEP_CID_RAD_TFPA_LUT,
                              ( LEP_ATTRIBUTE_T_PTR )radTFpaCLutPtr,
                              attributeWordLength );

   return( result );
}

/* Deprecated: Use LEP_GetRadTAuxLut */
LEP_RESULT LeptonSDKEmb32OEM::LEP_GetRadTAuxCLut( LEP_CAMERA_PORT_DESC_T_PTR portDescPtr,
                               LEP_RAD_LUT256_T_PTR radTAuxCLutPtr )
{
   LEP_RESULT result = LEP_OK;
   LEP_UINT16 attributeWordLength = 256;    // 256 16-bit word LUT

   if( radTAuxCLutPtr == NULL )
   {
      return( LEP_BAD_ARG_POINTER_ERROR );
   }
   result = LEP_GetAttribute(  portDescPtr,
                              ( LEP_COMMAND_ID )LEP_CID_RAD_TAUX_LUT,
                              ( LEP_ATTRIBUTE_T_PTR )radTAuxCLutPtr,
                              attributeWordLength );

   return( result );
}

/* Deprecated: Use LEP_SetRadTAuxLut */
LEP_RESULT LeptonSDKEmb32OEM::LEP_SetRadTAuxCLut( LEP_CAMERA_PORT_DESC_T_PTR portDescPtr,
                               LEP_RAD_LUT256_T_PTR radTAuxCLutPtr )
{
   LEP_RESULT result = LEP_OK;
   LEP_UINT16 attributeWordLength = 256;    // 256 16-bit word LUT

   if( radTAuxCLutPtr == NULL )
   {
      return( LEP_BAD_ARG_POINTER_ERROR );
   }
   result = LEP_SetAttribute( portDescPtr,
                              ( LEP_COMMAND_ID )LEP_CID_RAD_TAUX_LUT,
                              ( LEP_ATTRIBUTE_T_PTR )radTAuxCLutPtr,
                              attributeWordLength );

   return( result );
}

LEP_RESULT LeptonSDKEmb32OEM::LEP_GetRadTFpaLut( LEP_CAMERA_PORT_DESC_T_PTR portDescPtr,
                              LEP_RAD_LUT256_T_PTR radTFpaLutPtr )
{
   LEP_RESULT result = LEP_OK;
   LEP_UINT16 attributeWordLength = 256;    // 256 16-bit word LUT

   if( radTFpaLutPtr == NULL )
   {
      return( LEP_BAD_ARG_POINTER_ERROR );
   }
   result = LEP_GetAttribute(  portDescPtr,
                              ( LEP_COMMAND_ID )LEP_CID_RAD_TFPA_LUT,
                              ( LEP_ATTRIBUTE_T_PTR )radTFpaLutPtr,
                              attributeWordLength );

   return( result );
}


LEP_RESULT LeptonSDKEmb32OEM::LEP_SetRadTFpaLut( LEP_CAMERA_PORT_DESC_T_PTR portDescPtr,
                              LEP_RAD_LUT256_T_PTR radTFpaLutPtr )
{
   LEP_RESULT result = LEP_OK;
   LEP_UINT16 attributeWordLength = 256;    // 256 16-bit word LUT

   if( radTFpaLutPtr == NULL )
   {
      return( LEP_BAD_ARG_POINTER_ERROR );
   }
   result = LEP_SetAttribute( portDescPtr,
                              ( LEP_COMMAND_ID )LEP_CID_RAD_TFPA_LUT,
                              ( LEP_ATTRIBUTE_T_PTR )radTFpaLutPtr,
                              attributeWordLength );

   return( result );
}


LEP_RESULT LeptonSDKEmb32OEM::LEP_GetRadTAuxLut( LEP_CAMERA_PORT_DESC_T_PTR portDescPtr,
                              LEP_RAD_LUT256_T_PTR radTAuxLutPtr )
{
   LEP_RESULT result = LEP_OK;
   LEP_UINT16 attributeWordLength = 256;    // 256 16-bit word LUT

   if( radTAuxLutPtr == NULL )
   {
      return( LEP_BAD_ARG_POINTER_ERROR );
   }
   result = LEP_GetAttribute(  portDescPtr,
                              ( LEP_COMMAND_ID )LEP_CID_RAD_TAUX_LUT,
                              ( LEP_ATTRIBUTE_T_PTR )radTAuxLutPtr,
                              attributeWordLength );

   return( result );
}


LEP_RESULT LeptonSDKEmb32OEM::LEP_SetRadTAuxLut( LEP_CAMERA_PORT_DESC_T_PTR portDescPtr,
                              LEP_RAD_LUT256_T_PTR radTAuxLutPtr )
{
   LEP_RESULT result = LEP_OK;
   LEP_UINT16 attributeWordLength = 256;    // 256 16-bit word LUT

   if( radTAuxLutPtr == NULL )
   {
      return( LEP_BAD_ARG_POINTER_ERROR );
   }
   result = LEP_SetAttribute( portDescPtr,
                              ( LEP_COMMAND_ID )LEP_CID_RAD_TAUX_LUT,
                              ( LEP_ATTRIBUTE_T_PTR )radTAuxLutPtr,
                              attributeWordLength );

   return( result );
}


LEP_RESULT LeptonSDKEmb32OEM::LEP_GetRadResponsivityValueLut( LEP_CAMERA_PORT_DESC_T_PTR portDescPtr,
                                           LEP_RAD_LUT128_T_PTR radResponsivityValueLutPtr )
{
   LEP_RESULT result = LEP_OK;
   LEP_UINT16 attributeWordLength = 128;    // 128 16-bit word LUT

   if( radResponsivityValueLutPtr == NULL )
   {
      return( LEP_BAD_ARG_POINTER_ERROR );
   }
   result = LEP_GetAttribute(  portDescPtr,
                              ( LEP_COMMAND_ID )LEP_CID_RAD_RESPONSIVITY_VALUE_LUT,
                              ( LEP_ATTRIBUTE_T_PTR )radResponsivityValueLutPtr,
                              attributeWordLength );

   return( result );
}


LEP_RESULT LeptonSDKEmb32OEM::LEP_SetRadResponsivityValueLut( LEP_CAMERA_PORT_DESC_T_PTR portDescPtr,
                                           LEP_RAD_LUT128_T_PTR radResponsivityValueLutPtr )
{
   LEP_RESULT result = LEP_OK;
   LEP_UINT16 attributeWordLength = 128;    // 128 16-bit word LUT

   if( radResponsivityValueLutPtr == NULL )
   {
      return( LEP_BAD_ARG_POINTER_ERROR );
   }
   result = LEP_SetAttribute( portDescPtr,
                              ( LEP_COMMAND_ID )LEP_CID_RAD_RESPONSIVITY_VALUE_LUT,
                              ( LEP_ATTRIBUTE_T_PTR )radResponsivityValueLutPtr,
                              attributeWordLength );

   return( result );
}


LEP_RESULT LeptonSDKEmb32OEM::LEP_GetRadDebugTemp( LEP_CAMERA_PORT_DESC_T_PTR portDescPtr,
                                LEP_RAD_KELVIN_T_PTR radDebugTempPtr )
{
   LEP_RESULT result = LEP_OK;
   LEP_UINT16 attributeWordLength = 1;    // single 16-bit word

   if( radDebugTempPtr == NULL )
   {
      return( LEP_BAD_ARG_POINTER_ERROR );
   }
   result = LEP_GetAttribute(  portDescPtr,
                              ( LEP_COMMAND_ID )LEP_CID_RAD_DEBUG_TEMP,
                              ( LEP_ATTRIBUTE_T_PTR )radDebugTempPtr,
                              attributeWordLength );

   return( result );
}


LEP_RESULT LeptonSDKEmb32OEM::LEP_SetRadDebugTemp( LEP_CAMERA_PORT_DESC_T_PTR portDescPtr,
                                LEP_RAD_KELVIN_T radDebugTemp )
{
   LEP_RESULT result = LEP_OK;
   LEP_UINT16 attributeWordLength = 1; /* single 16-bit value */

   result = LEP_SetAttribute( portDescPtr,
                              ( LEP_COMMAND_ID )LEP_CID_RAD_DEBUG_TEMP,
                              ( LEP_ATTRIBUTE_T_PTR ) & radDebugTemp,
                              attributeWordLength );

   return( result );
}


LEP_RESULT LeptonSDKEmb32OEM::LEP_GetRadDebugFlux( LEP_CAMERA_PORT_DESC_T_PTR portDescPtr,
                                LEP_RAD_FLUX_T_PTR radDebugFluxPtr )
{
   LEP_RESULT result = LEP_OK;
   LEP_UINT16 attributeWordLength = 2;    // 2 16-bit words

   if( radDebugFluxPtr == NULL )
   {
      return( LEP_BAD_ARG_POINTER_ERROR );
   }
   result = LEP_GetAttribute(  portDescPtr,
                              ( LEP_COMMAND_ID )LEP_CID_RAD_DEBUG_FLUX,
                              ( LEP_ATTRIBUTE_T_PTR )radDebugFluxPtr,
                              attributeWordLength );

   return( result );
}


LEP_RESULT LeptonSDKEmb32OEM::LEP_SetRadDebugFlux( LEP_CAMERA_PORT_DESC_T_PTR portDescPtr,
                                LEP_RAD_FLUX_T radDebugFlux )
{
   LEP_RESULT result = LEP_OK;
   LEP_UINT16 attributeWordLength = 2;    // 2 16-bit words

   _LEP_data[1] = radDebugFlux >> 16;
   _LEP_data[0] = radDebugFlux & 0xFFFF;

   result = LEP_SetAttribute( portDescPtr,
                              ( LEP_COMMAND_ID )LEP_CID_RAD_DEBUG_FLUX,
                              ( LEP_ATTRIBUTE_T_PTR ) & _LEP_data,
                              attributeWordLength );

   return( result );
}


LEP_RESULT LeptonSDKEmb32OEM::LEP_GetRadEnableState( LEP_CAMERA_PORT_DESC_T_PTR portDescPtr,
                                  LEP_RAD_ENABLE_E_PTR radEnableStatePtr )
{
   LEP_RESULT result = LEP_OK;
   LEP_UINT16 attributeWordLength = 2;    // 2 16-bit words for an enum

   if( radEnableStatePtr == NULL )
   {
      return( LEP_BAD_ARG_POINTER_ERROR );
   }
   result = LEP_GetAttribute(  portDescPtr,
                              ( LEP_COMMAND_ID )LEP_CID_RAD_ENABLE_STATE,
                              ( LEP_ATTRIBUTE_T_PTR )radEnableStatePtr,
                              attributeWordLength );

   return( result );
}


LEP_RESULT LeptonSDKEmb32OEM::LEP_SetRadEnableState( LEP_CAMERA_PORT_DESC_T_PTR portDescPtr,
                                  LEP_RAD_ENABLE_E radEnableState )
{
   LEP_RESULT result = LEP_OK;
   LEP_UINT16 attributeWordLength = 2;    // 2 16-bit words for an enum

   _LEP_data[1] = 0;
   _LEP_data[0] = (LEP_UINT16) radEnableState;

   result = LEP_SetAttribute( portDescPtr,
                              ( LEP_COMMAND_ID )LEP_CID_RAD_ENABLE_STATE,
                              ( LEP_ATTRIBUTE_T_PTR ) & _LEP_data,
                              attributeWordLength );

   return( result );
}


LEP_RESULT LeptonSDKEmb32OEM::LEP_GetRadGlobalGain( LEP_CAMERA_PORT_DESC_T_PTR portDescPtr,
                                 LEP_RAD_GLOBAL_GAIN_T_PTR radGlobalGainPtr )
{
   LEP_RESULT result = LEP_OK;
   LEP_UINT16 attributeWordLength = 1;    // single 16-bit word

   if( radGlobalGainPtr == NULL )
   {
      return( LEP_BAD_ARG_POINTER_ERROR );
   }
   result = LEP_GetAttribute(  portDescPtr,
                              ( LEP_COMMAND_ID )LEP_CID_RAD_GLOBAL_GAIN,
                              ( LEP_ATTRIBUTE_T_PTR )radGlobalGainPtr,
                              attributeWordLength );

   return( result );
}


LEP_RESULT LeptonSDKEmb32OEM::LEP_SetRadGlobalGain( LEP_CAMERA_PORT_DESC_T_PTR portDescPtr,
                                 LEP_RAD_GLOBAL_GAIN_T radGlobalGain )
{
   LEP_RESULT result = LEP_OK;
   LEP_UINT16 attributeWordLength = 1; /* single 16-bit value */

   result = LEP_SetAttribute( portDescPtr,
                              ( LEP_COMMAND_ID )LEP_CID_RAD_GLOBAL_GAIN,
                              ( LEP_ATTRIBUTE_T_PTR ) & radGlobalGain,
                              attributeWordLength );

   return( result );
}


LEP_RESULT LeptonSDKEmb32OEM::LEP_GetRadGlobalOffset( LEP_CAMERA_PORT_DESC_T_PTR portDescPtr,
                                   LEP_RAD_GLOBAL_OFFSET_T_PTR radGlobalOffsetPtr )
{
   LEP_RESULT result = LEP_OK;
   LEP_UINT16 attributeWordLength = 1;    // single 16-bit word

   if( radGlobalOffsetPtr == NULL )
   {
      return( LEP_BAD_ARG_POINTER_ERROR );
   }
   result = LEP_GetAttribute(  portDescPtr,
                              ( LEP_COMMAND_ID )LEP_CID_RAD_GLOBAL_OFFSET,
                              ( LEP_ATTRIBUTE_T_PTR )radGlobalOffsetPtr,
                              attributeWordLength );

   return( result );
}


LEP_RESULT LeptonSDKEmb32OEM::LEP_SetRadGlobalOffset( LEP_CAMERA_PORT_DESC_T_PTR portDescPtr,
                                   LEP_RAD_GLOBAL_OFFSET_T radGlobalOffset )
{
   LEP_RESULT result = LEP_OK;
   LEP_UINT16 attributeWordLength = 1; /* single 16-bit value */

   result = LEP_SetAttribute( portDescPtr,
                              ( LEP_COMMAND_ID )LEP_CID_RAD_GLOBAL_OFFSET,
                              ( LEP_ATTRIBUTE_T_PTR ) & radGlobalOffset,
                              attributeWordLength );

   return( result );
}


LEP_RESULT LeptonSDKEmb32OEM::LEP_GetRadTFpaCtsMode( LEP_CAMERA_PORT_DESC_T_PTR portDescPtr,
                                  LEP_RAD_TEMPERATURE_UPDATE_E_PTR radTFpaCtsModePtr )
{
   LEP_RESULT result = LEP_OK;
   LEP_UINT16 attributeWordLength = 2;    // 2 16-bit words for an enum

   if( radTFpaCtsModePtr == NULL )
   {
      return( LEP_BAD_ARG_POINTER_ERROR );
   }
   result = LEP_GetAttribute(  portDescPtr,
                              ( LEP_COMMAND_ID )LEP_CID_RAD_TFPA_CTS_MODE,
                              ( LEP_ATTRIBUTE_T_PTR )radTFpaCtsModePtr,
                              attributeWordLength );

   return( result );
}


LEP_RESULT LeptonSDKEmb32OEM::LEP_SetRadTFpaCtsMode( LEP_CAMERA_PORT_DESC_T_PTR portDescPtr,
                                  LEP_RAD_TEMPERATURE_UPDATE_E radTFpaCtsMode )
{
   LEP_RESULT result = LEP_OK;
   LEP_UINT16 attributeWordLength = 2;    // 2 16-bit words for an enum

   _LEP_data[1] = 0;
   _LEP_data[0] = (LEP_UINT16) radTFpaCtsMode;

   result = LEP_SetAttribute( portDescPtr,
                              ( LEP_COMMAND_ID )LEP_CID_RAD_TFPA_CTS_MODE,
                              ( LEP_ATTRIBUTE_T_PTR ) & _LEP_data,
                              attributeWordLength );

   return( result );
}


LEP_RESULT LeptonSDKEmb32OEM::LEP_GetRadTAuxCtsMode( LEP_CAMERA_PORT_DESC_T_PTR portDescPtr,
                                  LEP_RAD_TEMPERATURE_UPDATE_E_PTR radTAuxCtsModePtr )
{
   LEP_RESULT result = LEP_OK;
   LEP_UINT16 attributeWordLength = 2;    // 2 16-bit words for an enum

   if( radTAuxCtsModePtr == NULL )
   {
      return( LEP_BAD_ARG_POINTER_ERROR );
   }
   result = LEP_GetAttribute(  portDescPtr,
                              ( LEP_COMMAND_ID )LEP_CID_RAD_TAUX_CTS_MODE,
                              ( LEP_ATTRIBUTE_T_PTR )radTAuxCtsModePtr,
                              attributeWordLength );

   return( result );
}
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
